serhalahmad/unibots/src/simulation/webots-files/main-env/april-tags/tag-0.png

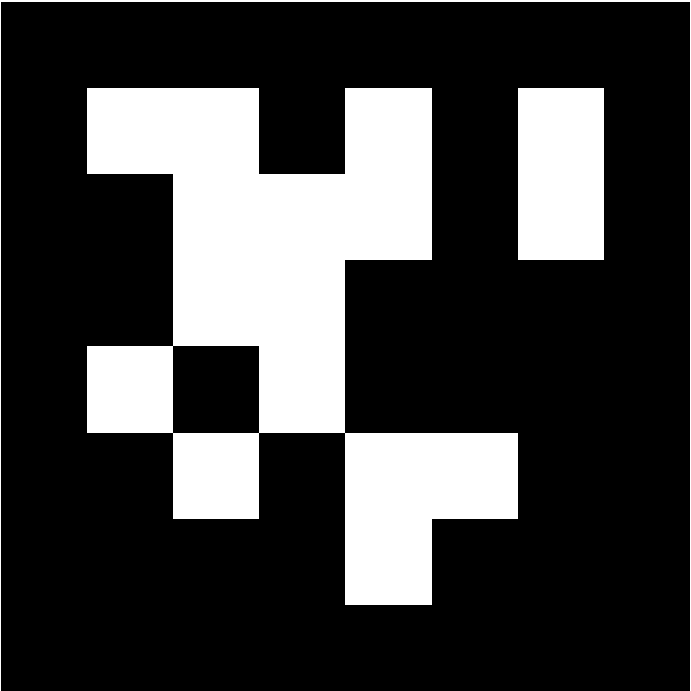
src/simulation/webots-files/main-env/april-tags/tag-0.png
