serhalahmad/unibots/src/simulation/webots-files/main-env/april-tags/tag-2.png

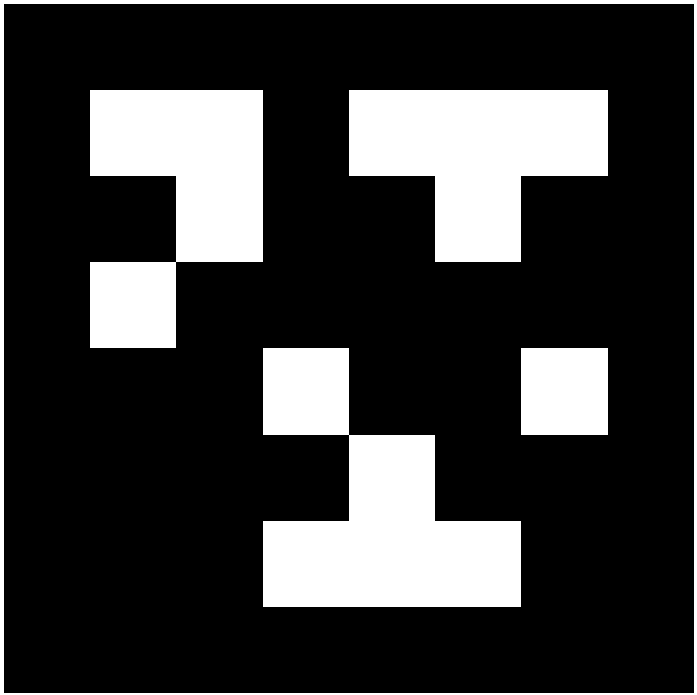
src/simulation/webots-files/main-env/april-tags/tag-2.png
