serhalahmad/unibots/src/simulation/webots-files/main-env/april-tags/tag-3.png

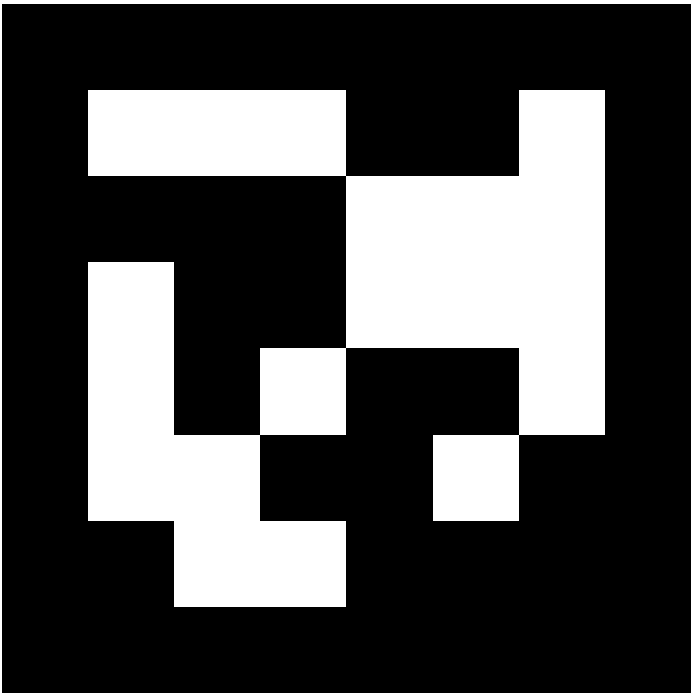
src/simulation/webots-files/main-env/april-tags/tag-3.png
