serhalahmad/unibots/src/simulation/webots-files/main-env/april-tags/tag-4.png

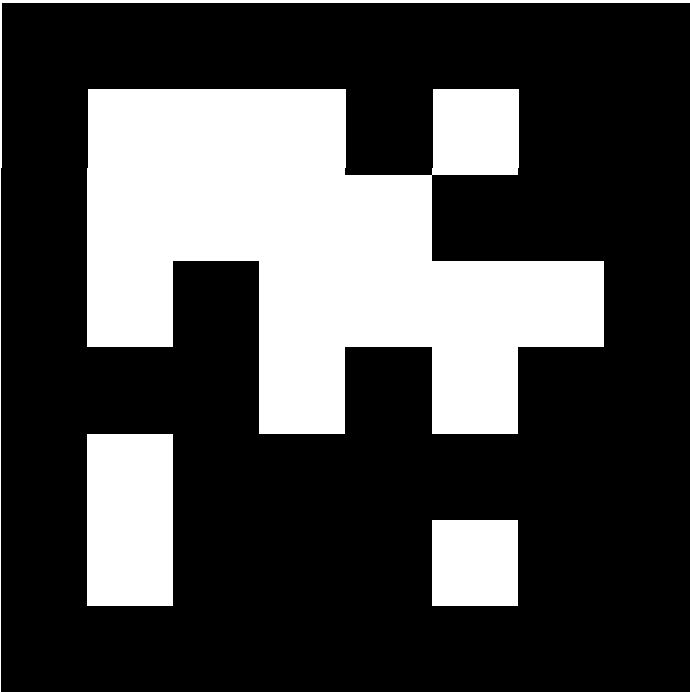
src/simulation/webots-files/main-env/april-tags/tag-4.png
