serhalahmad/unibots/src/simulation/webots-files/main-env/april-tags/tag-5.png

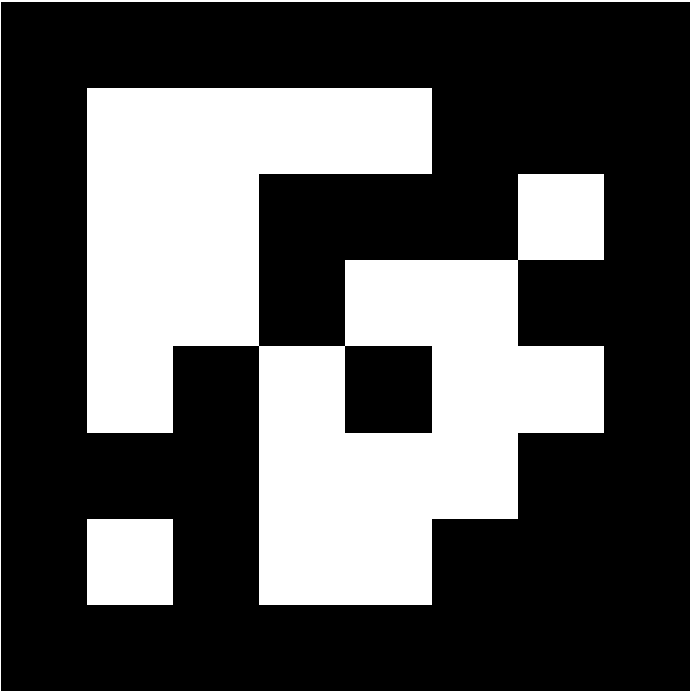
src/simulation/webots-files/main-env/april-tags/tag-5.png
