serhalahmad/unibots/src/simulation/webots-files/main-env/april-tags/tag-6.png

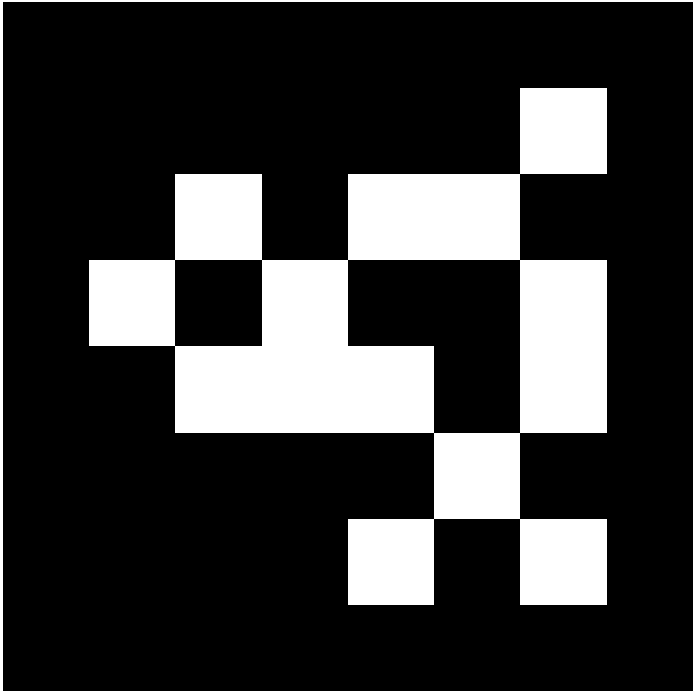
src/simulation/webots-files/main-env/april-tags/tag-6.png
