serhalahmad/unibots/src/simulation/webots-files/main-env/april-tags/tag-7.png

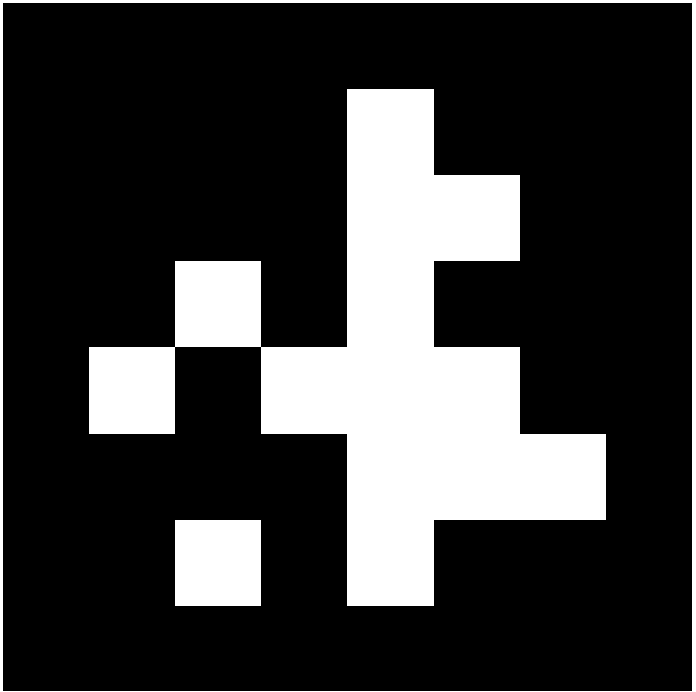
src/simulation/webots-files/main-env/april-tags/tag-7.png
