serhalahmad/unibots/src/simulation/webots-files/main-env/april-tags/tag-8.png

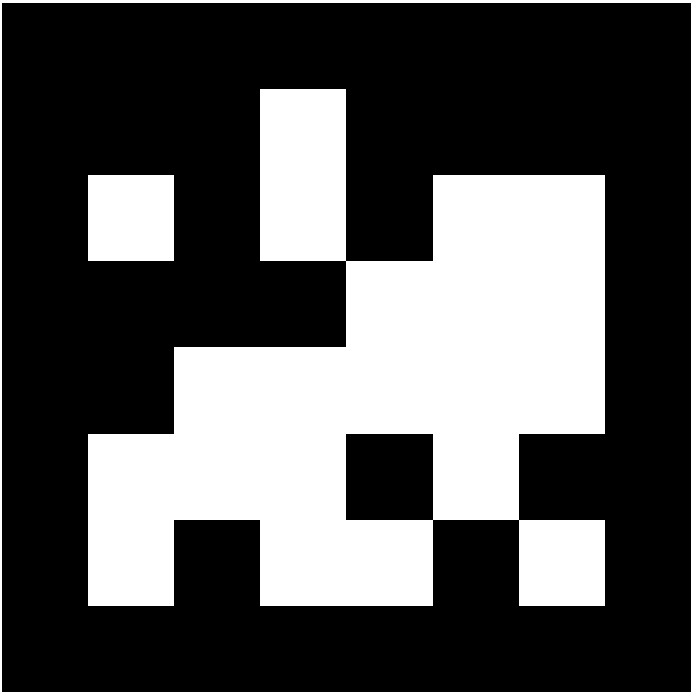
src/simulation/webots-files/main-env/april-tags/tag-8.png
