serhalahmad/unibots/src/simulation/webots-files/main-env/april-tags/tag-9.png

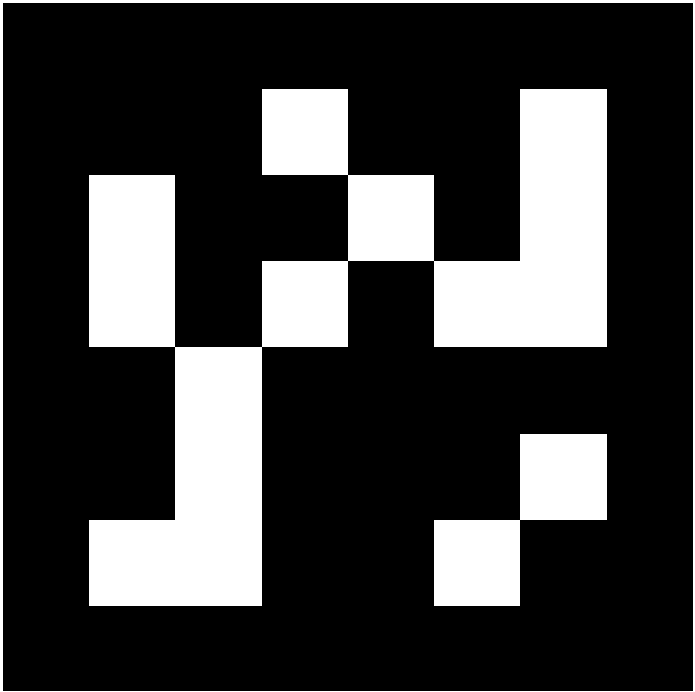
src/simulation/webots-files/main-env/april-tags/tag-9.png
