serhalahmad/unibots/src/simulation/webots-files/main-env/april-tags/tag-10.png

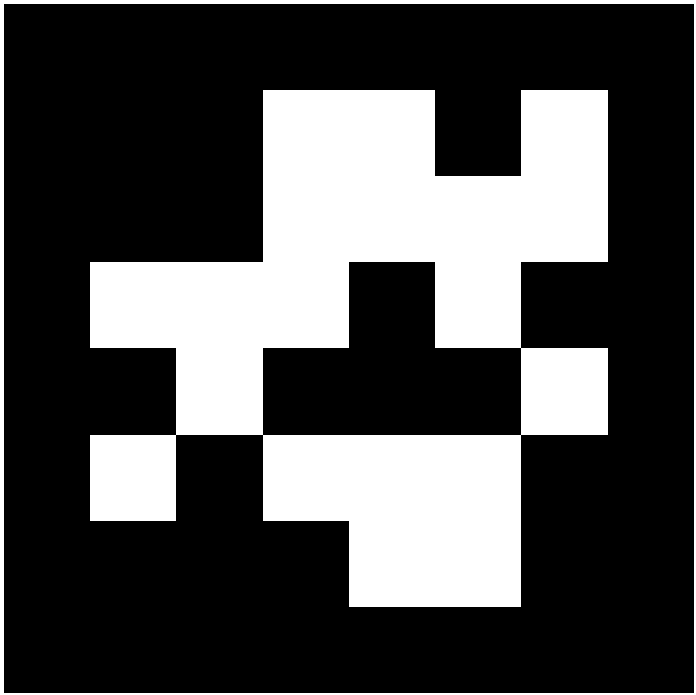
src/simulation/webots-files/main-env/april-tags/tag-10.png
