serhalahmad/unibots/src/simulation/webots-files/main-env/april-tags/tag-11.png

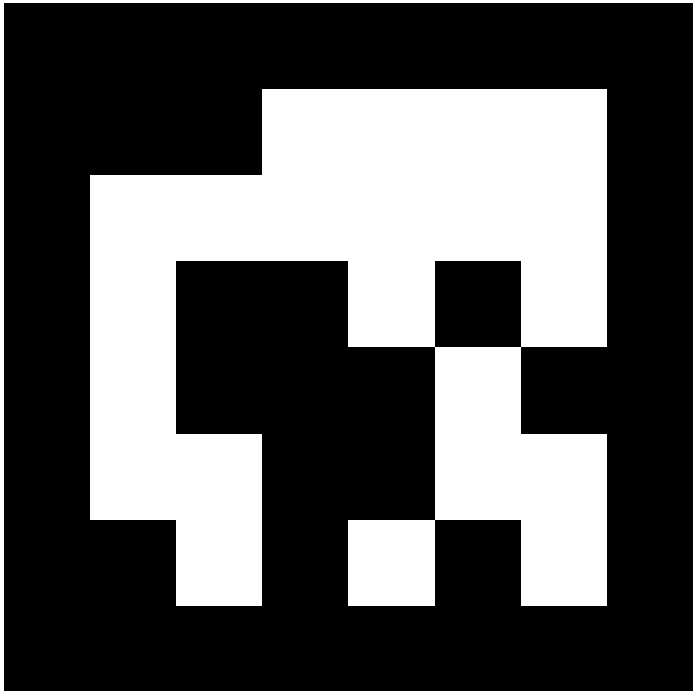
src/simulation/webots-files/main-env/april-tags/tag-11.png
