serhalahmad/unibots/src/simulation/webots-files/main-env/april-tags/tag-12.png

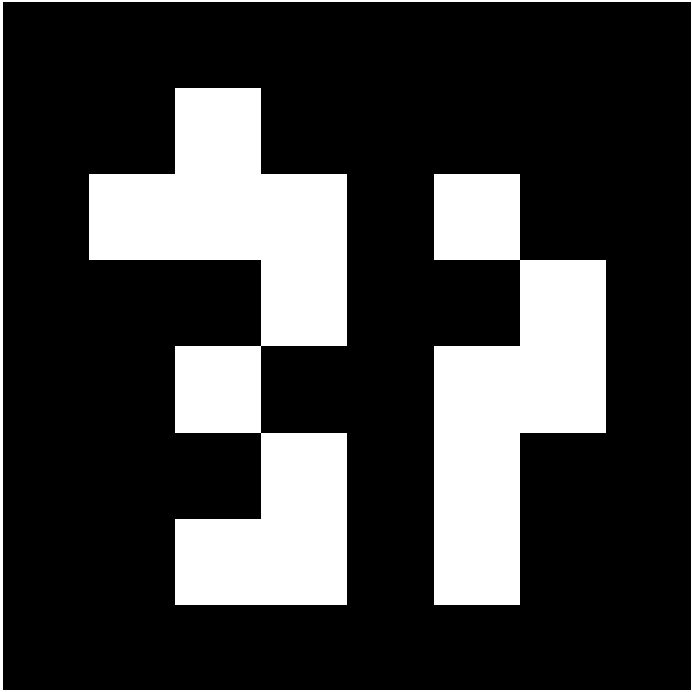
src/simulation/webots-files/main-env/april-tags/tag-12.png
