serhalahmad/unibots/src/simulation/webots-files/main-env/april-tags/tag-14.png

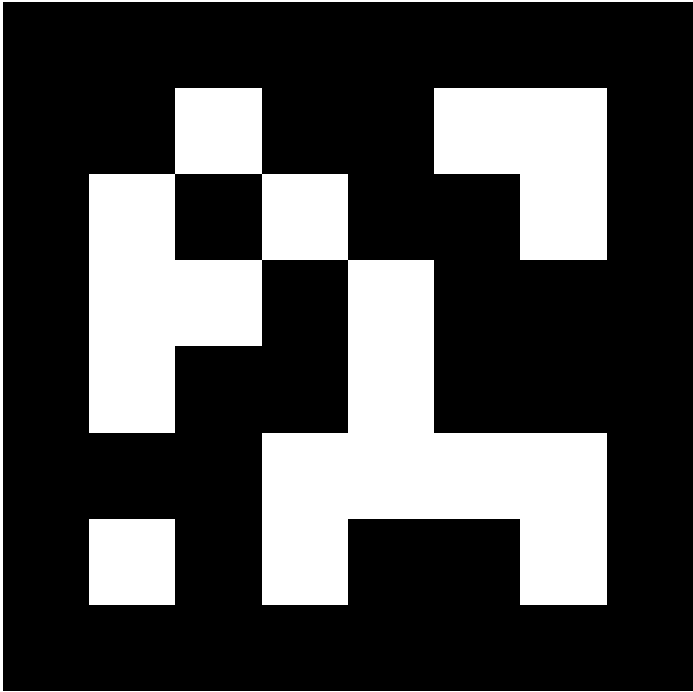
src/simulation/webots-files/main-env/april-tags/tag-14.png
