serhalahmad/unibots/src/simulation/webots-files/main-env/april-tags/tag-15.png

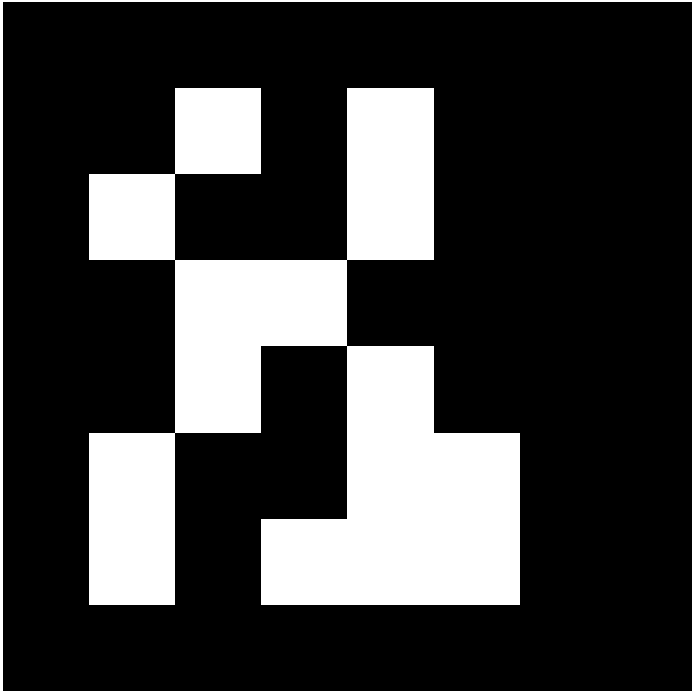
src/simulation/webots-files/main-env/april-tags/tag-15.png
