serhalahmad/unibots/src/simulation/webots-files/main-env/april-tags/tag-17.png

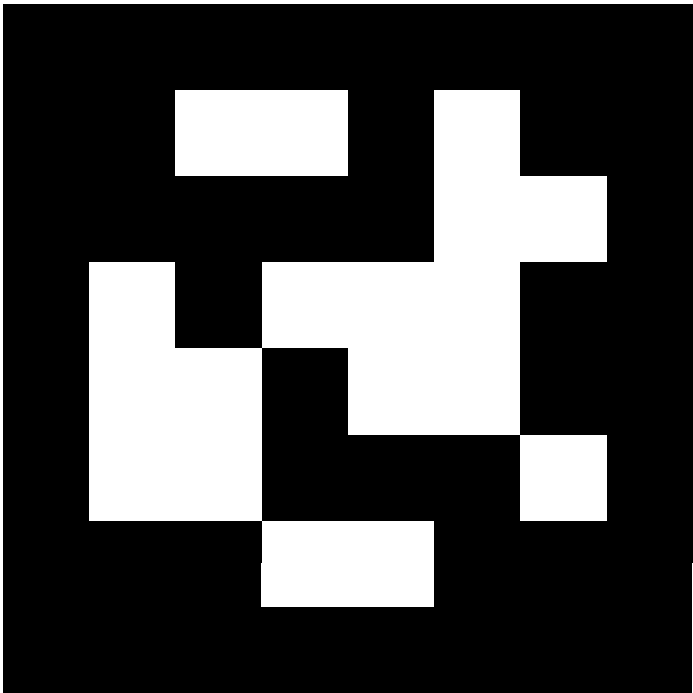
src/simulation/webots-files/main-env/april-tags/tag-17.png
