serhalahmad/unibots/src/simulation/webots-files/main-env/april-tags/tag-18.png

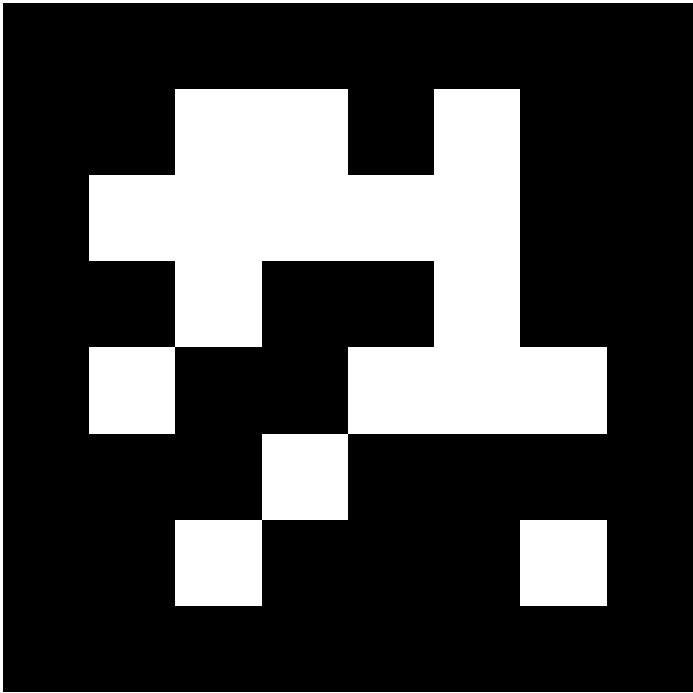
src/simulation/webots-files/main-env/april-tags/tag-18.png
