serhalahmad/unibots/src/simulation/webots-files/main-env/april-tags/tag-19.png

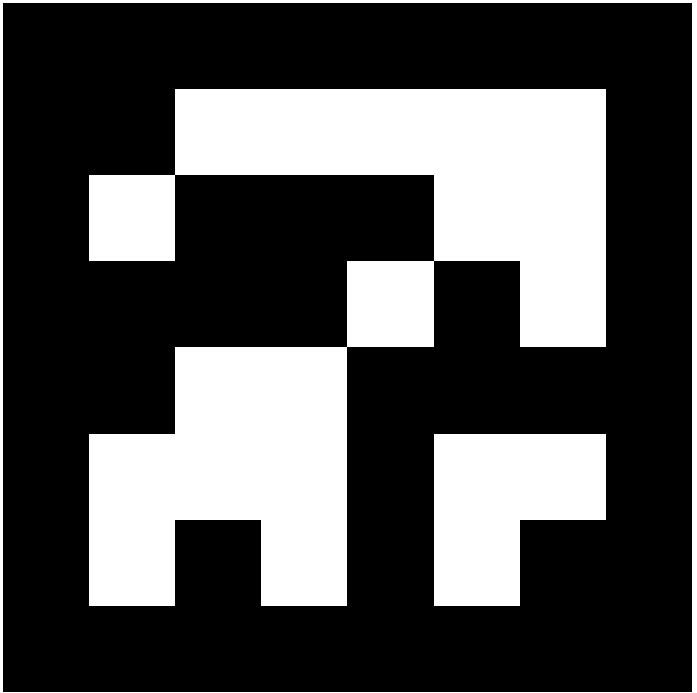
src/simulation/webots-files/main-env/april-tags/tag-19.png
