serhalahmad/unibots/src/simulation/webots-files/main-env/april-tags/tag-20.png

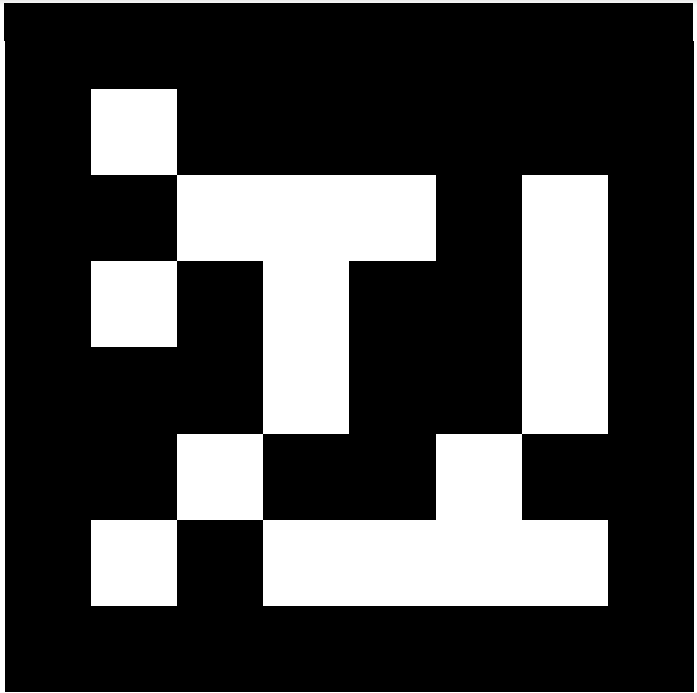
src/simulation/webots-files/main-env/april-tags/tag-20.png
