serhalahmad/unibots/src/simulation/webots-files/main-env/april-tags/tag-22.png

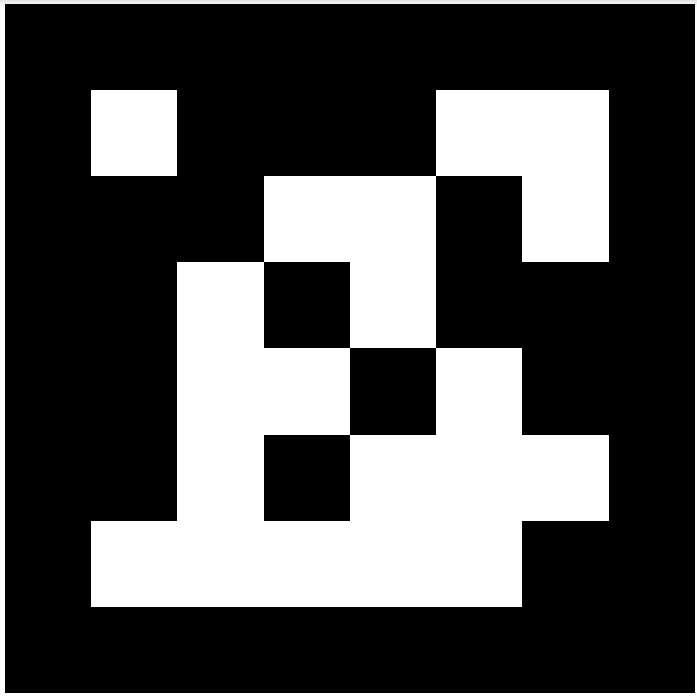
src/simulation/webots-files/main-env/april-tags/tag-22.png
