serhalahmad/unibots/cad-files/servo/mg-996r-servo-motor-1.snapshot.23/Parts/MG996R Motor.SLDPRT

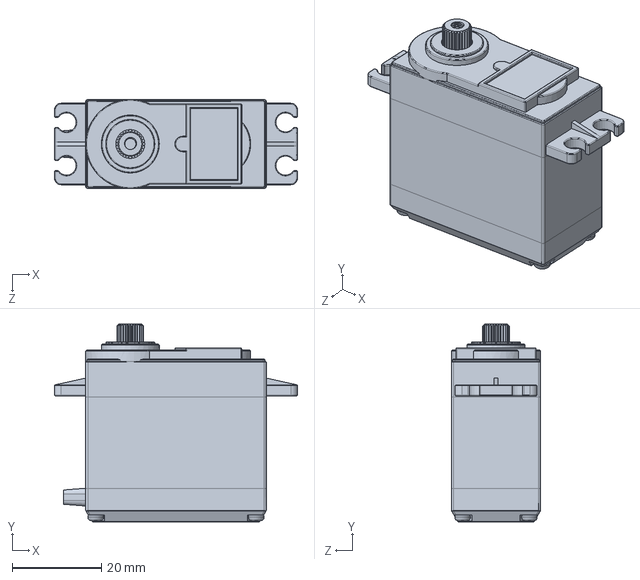
[picture p48: CAD file, 2025-01-23]
cad-files/servo/mg-996r-servo-motor-1.snapshot.23/Parts/MG996R Motor.SLDPRT
54.5 x 44.4 x 20.0 mm
