serhalahmad/unibots/cad-files/tire.SLDPRT

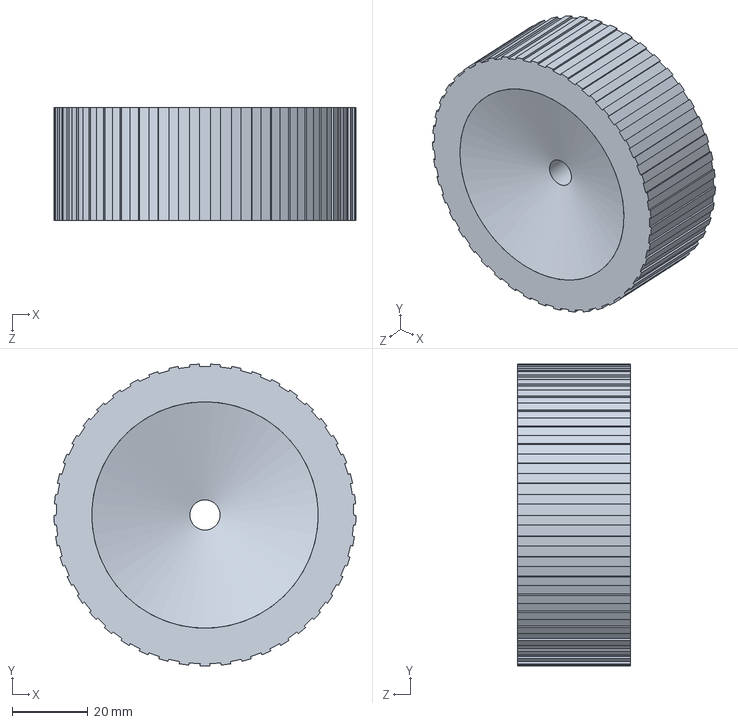
[picture p49: CAD file, 2025-01-23]
cad-files/tire.SLDPRT
80.0 x 80.0 x 30.0 mm
