serhalahmad/unibots/cad-files/unibots chassis/beam.STL.SLDPRT

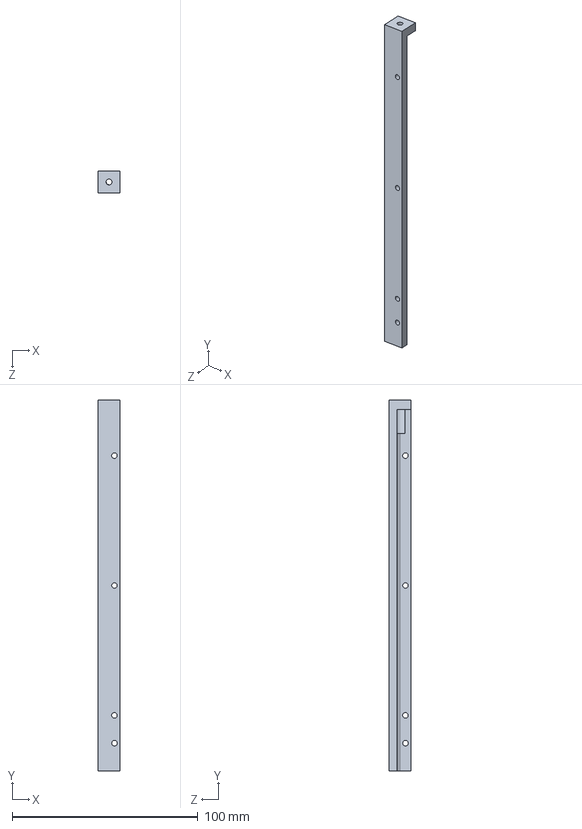
[picture p50: CAD file, 2025-03-25]
cad-files/unibots chassis/beam.STL.SLDPRT
12.0 x 200.0 x 12.0 mm
