serhalahmad/unibots/cad-files/unibots chassis/dxf files/componentsfloor.DXF

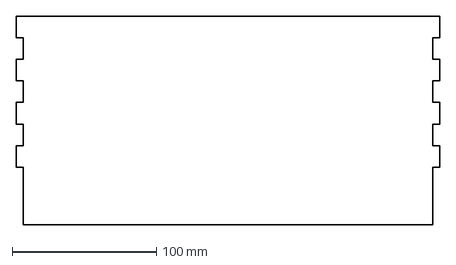
[picture p51: CAD file, 2025-03-25]
cad-files/unibots chassis/dxf files/componentsfloor.DXF
294.0 x 145.0 mm
