serhalahmad/unibots/cad-files/unibots v1/tire og.SLDPRT

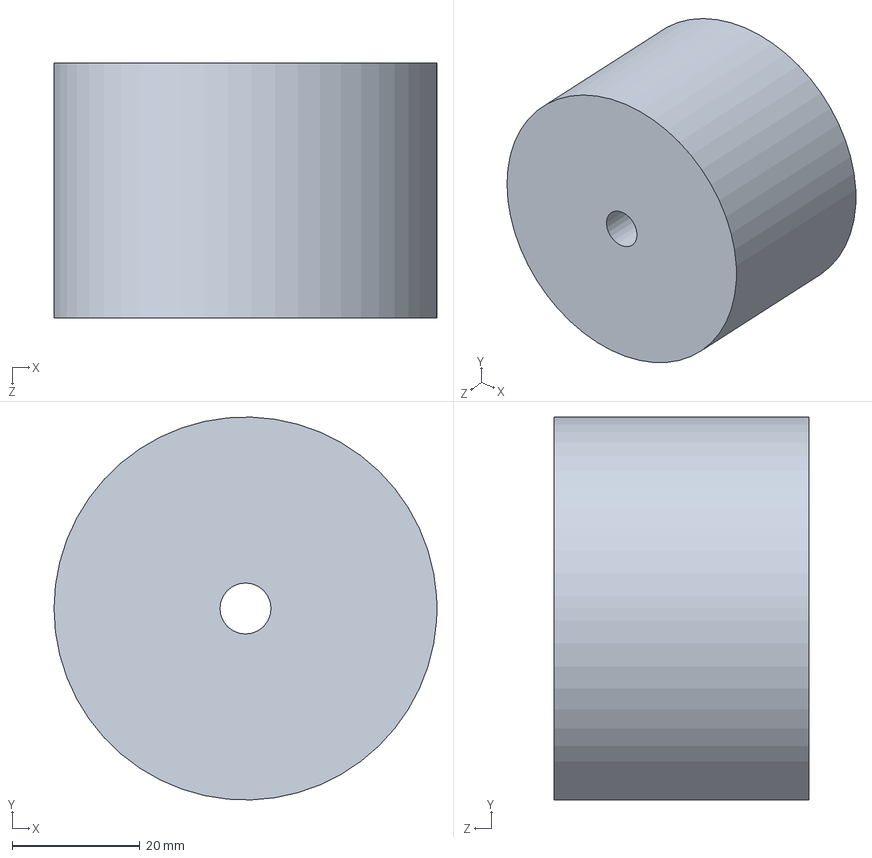
[picture p52: CAD file, 2025-01-23]
cad-files/unibots v1/tire og.SLDPRT
60.0 x 60.0 x 40.0 mm
