serhalahmad/unibots/src/simulation/webots-files/main-env/objects/rugby-ball.obj

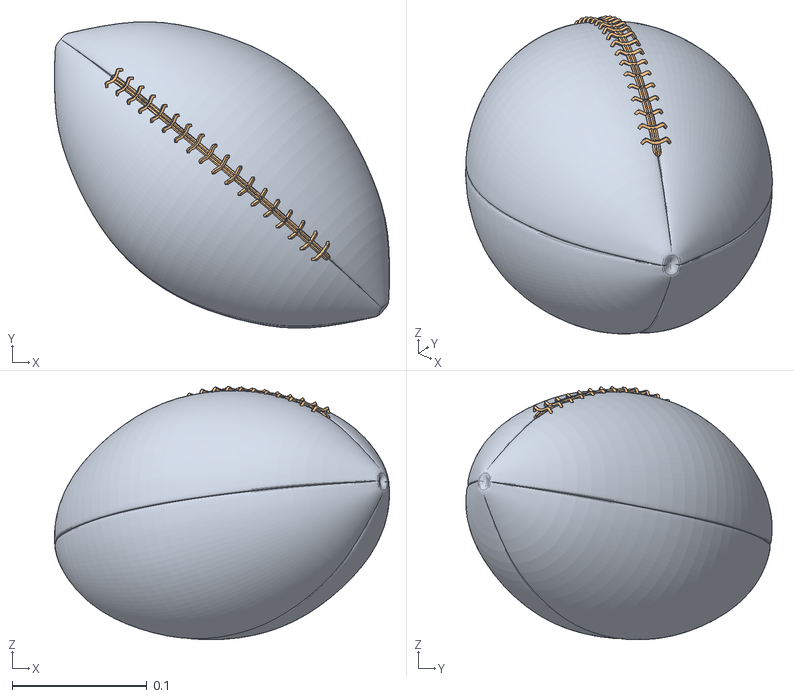
[picture p53: CAD file, 2025-06-17]
src/simulation/webots-files/main-env/objects/rugby-ball.obj
0.249 x 0.228 x 0.188
American_Football_ball_1_Cylinder
American_Football_ball_2_BezierCurve
