serhalahmad/unibots/cad-files/gearbox test/Part4.SLDPRT

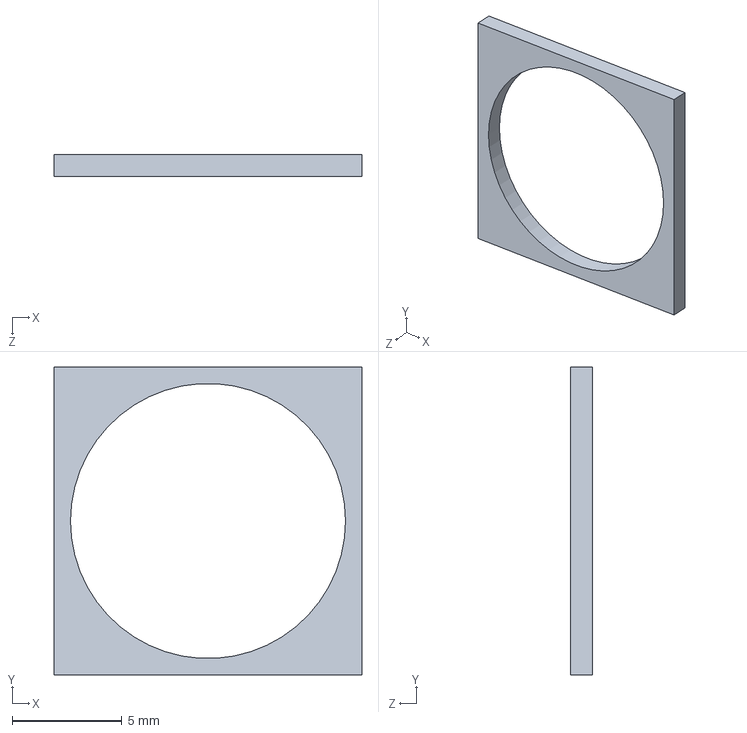
[picture p54: CAD file, 2025-02-14]
cad-files/gearbox test/Part4.SLDPRT
14.0 x 14.0 x 1.00 mm
