serhalahmad/unibots/cad-files/motor/worm-gear-motor-high-torque-12v-dc-motor-1.snapshot.1/Worm Gear Motor.SLDPRT

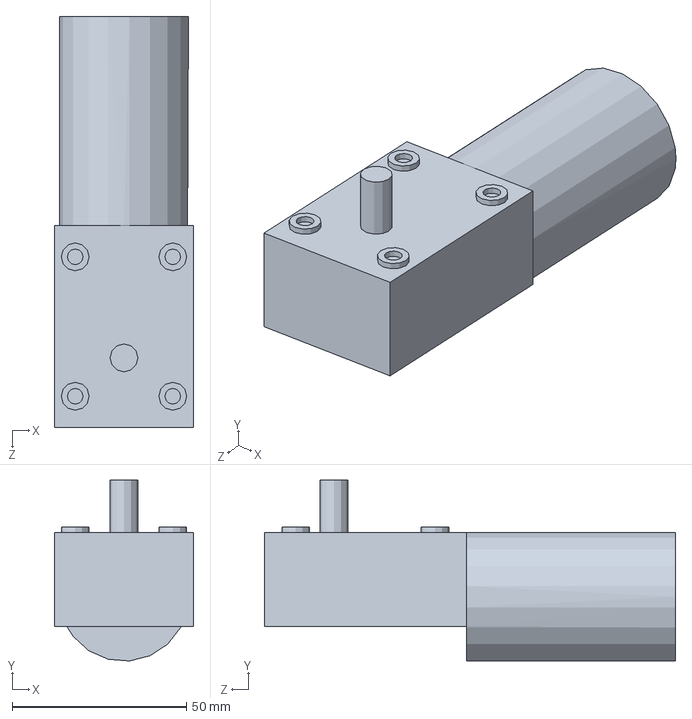
[picture p55: CAD file, 2025-01-23]
cad-files/motor/worm-gear-motor-high-torque-12v-dc-motor-1.snapshot.1/Worm Gear Motor.SLDPRT
40.0 x 51.9 x 118.0 mm
