serhalahmad/unibots/cad-files/New folder/chassis.STL

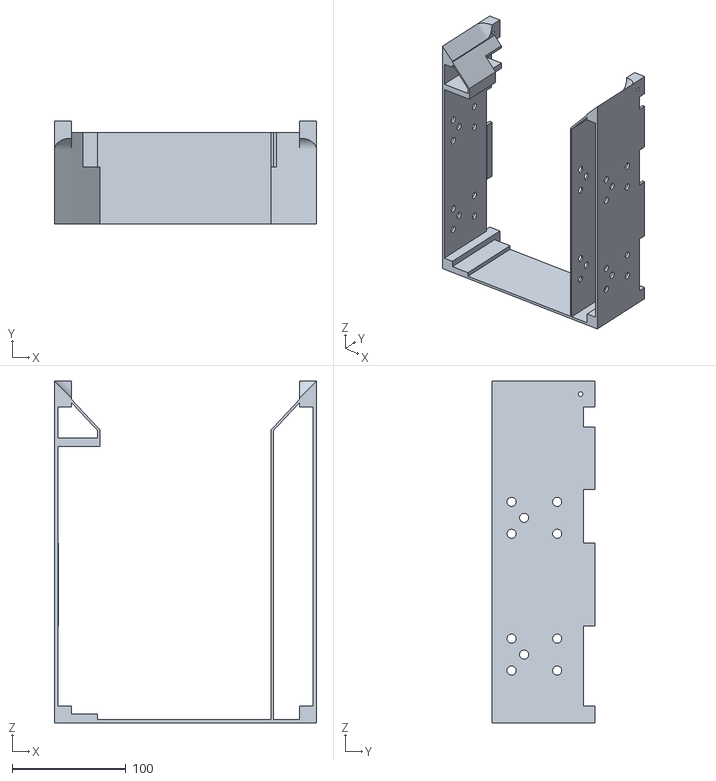
[picture p56: CAD file, 2025-01-28]
cad-files/New folder/chassis.STL
230.0 x 90.0 x 300.0
