serhalahmad/unibots/cad-files/servo/mg-996r-servo-motor-1.snapshot.23/Parts/circular horn.SLDPRT

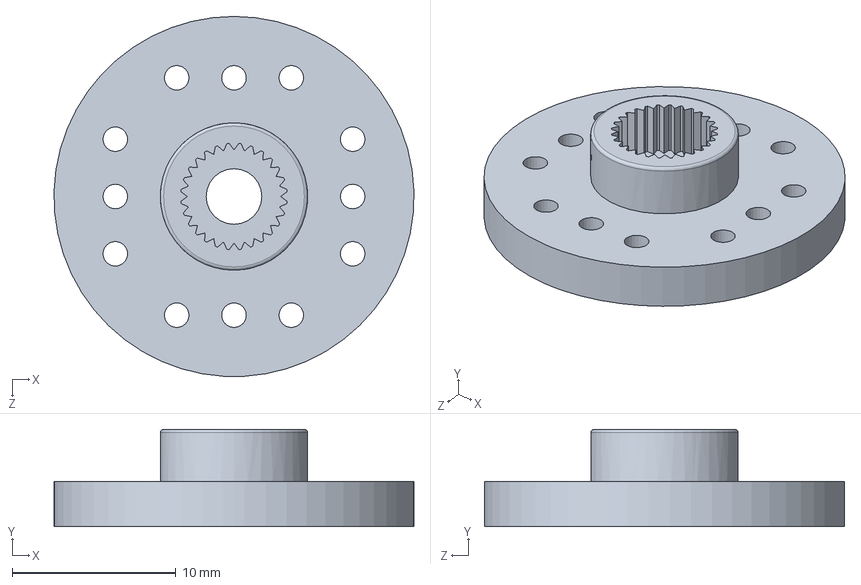
[picture p57: CAD file, 2025-01-23]
cad-files/servo/mg-996r-servo-motor-1.snapshot.23/Parts/circular horn.SLDPRT
22.0 x 5.95 x 22.0 mm
