serhalahmad/unibots/cad-files/unibots chassis/dxf files/rugbywall2.DXF

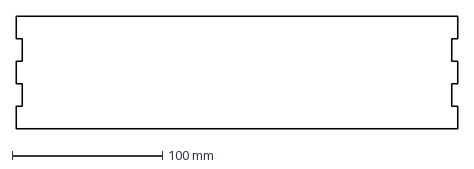
[picture p58: CAD file, 2025-03-25]
cad-files/unibots chassis/dxf files/rugbywall2.DXF
294.0 x 75.0 mm
