serhalahmad/unibots/cad-files/unibots chassis/rugbywall1.SLDPRT

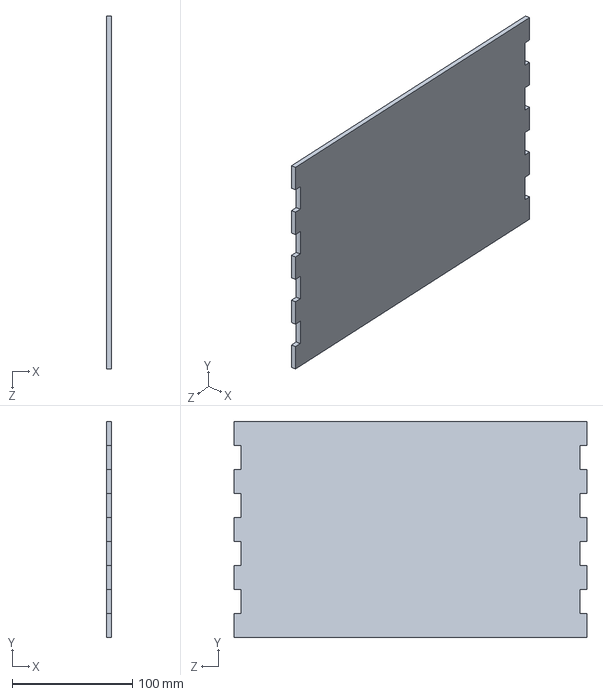
[picture p59: CAD file, 2025-03-25]
cad-files/unibots chassis/rugbywall1.SLDPRT
4.00 x 180.0 x 294.0 mm
