serhalahmad/unibots/cad-files/unibots v1/testclamp.SLDPRT

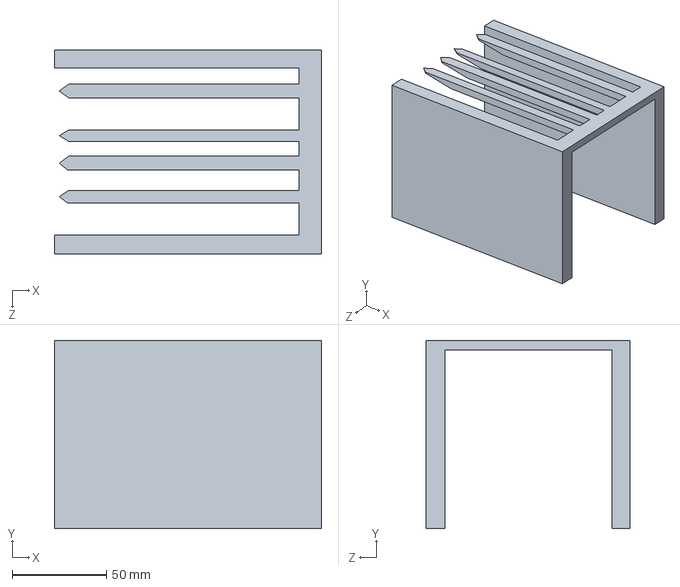
[picture p60: CAD file, 2025-01-23]
cad-files/unibots v1/testclamp.SLDPRT
141.8 x 100.0 x 108.3 mm
