serhalahmad/unibots/cad-files/door.SLDPRT

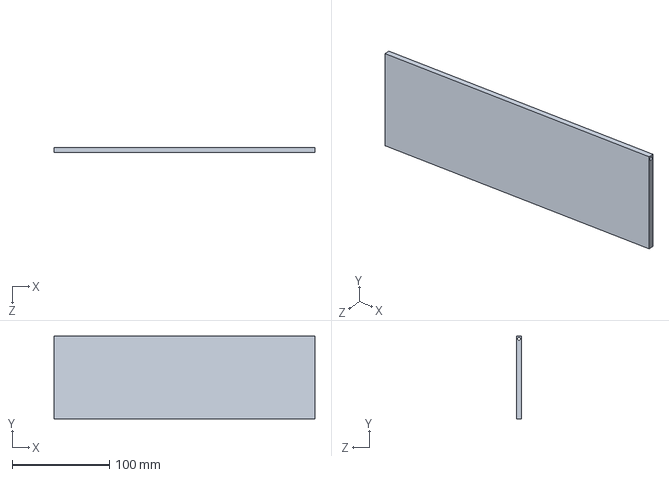
[picture p61: CAD file, 2025-01-23]
cad-files/door.SLDPRT
268.0 x 85.0 x 5.00 mm
