serhalahmad/unibots/cad-files/gearbox test/6_30mm shaft.STL

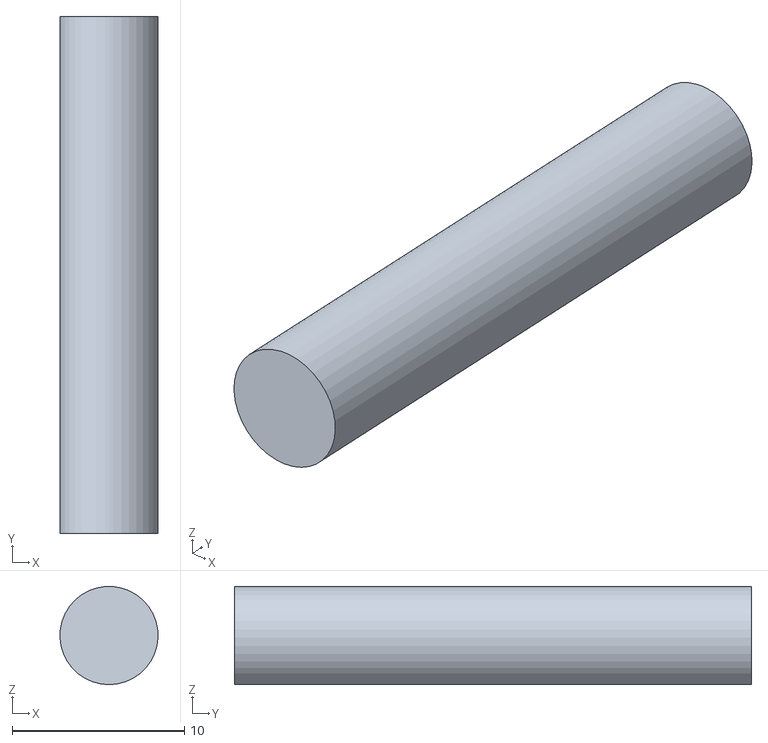
[picture p62: CAD file, 2025-02-14]
cad-files/gearbox test/6_30mm shaft.STL
5.69 x 30.0 x 5.70
