serhalahmad/unibots/cad-files/servo/mg-996r-servo-motor-1.snapshot.23/Parts/2-star horn.SLDPRT

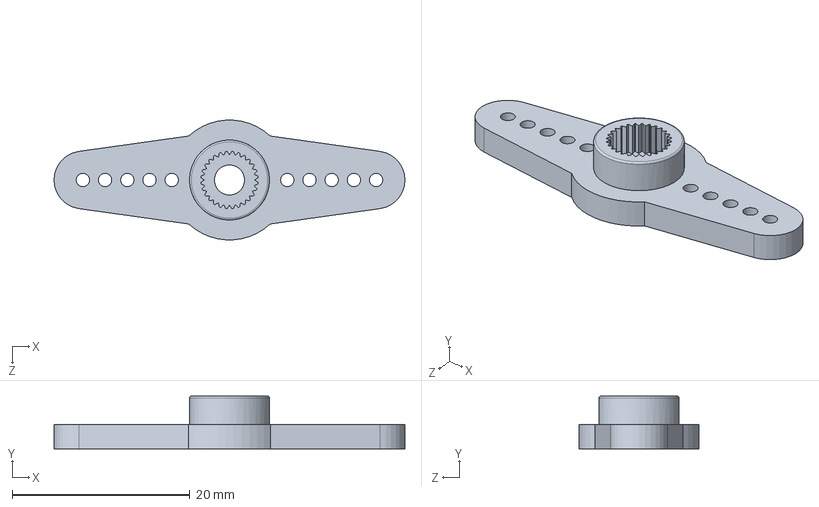
[picture p63: CAD file, 2025-01-23]
cad-files/servo/mg-996r-servo-motor-1.snapshot.23/Parts/2-star horn.SLDPRT
39.5 x 5.95 x 13.5 mm
