serhalahmad/unibots/cad-files/unibots chassis/dxf files/sidewalls.DXF

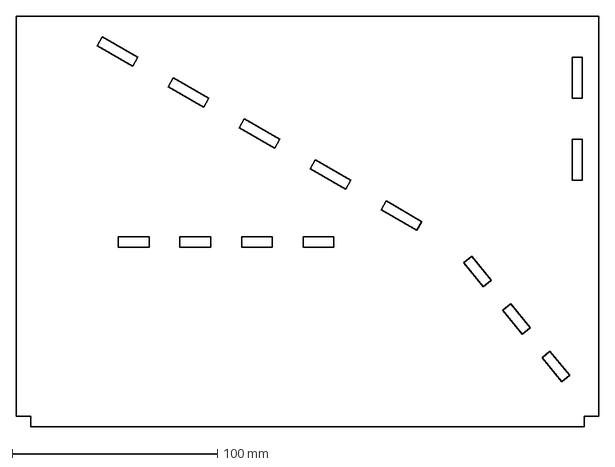
[picture p64: CAD file, 2025-03-25]
cad-files/unibots chassis/dxf files/sidewalls.DXF
284.0 x 200.0 mm
