serhalahmad/unibots/cad-files/17_1_25 rugby.SLDPRT

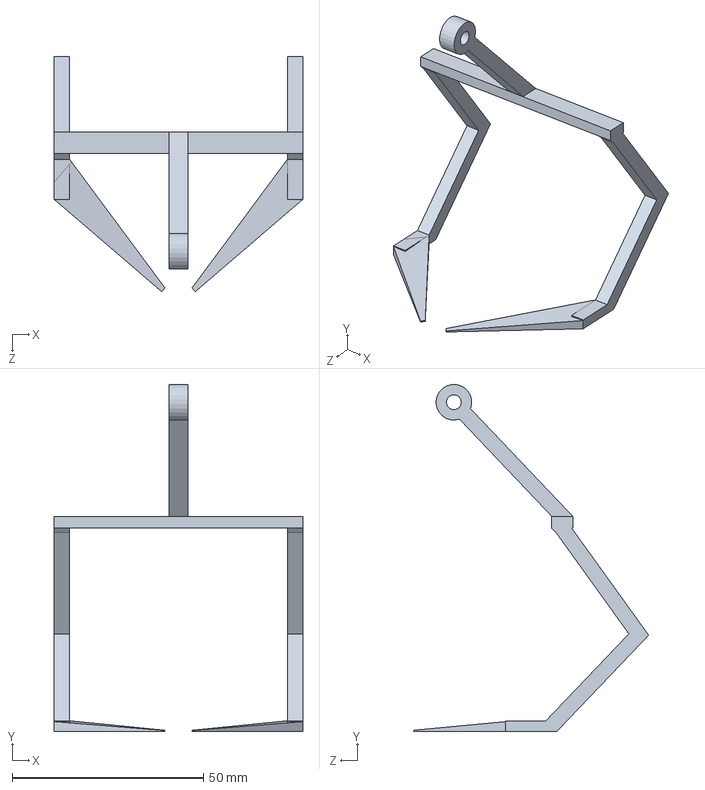
[picture p65: CAD file, 2025-01-23]
cad-files/17_1_25 rugby.SLDPRT
65.0 x 90.8 x 61.6 mm
