serhalahmad/unibots/cad-files/unibots chassis/layer1plate.SLDPRT

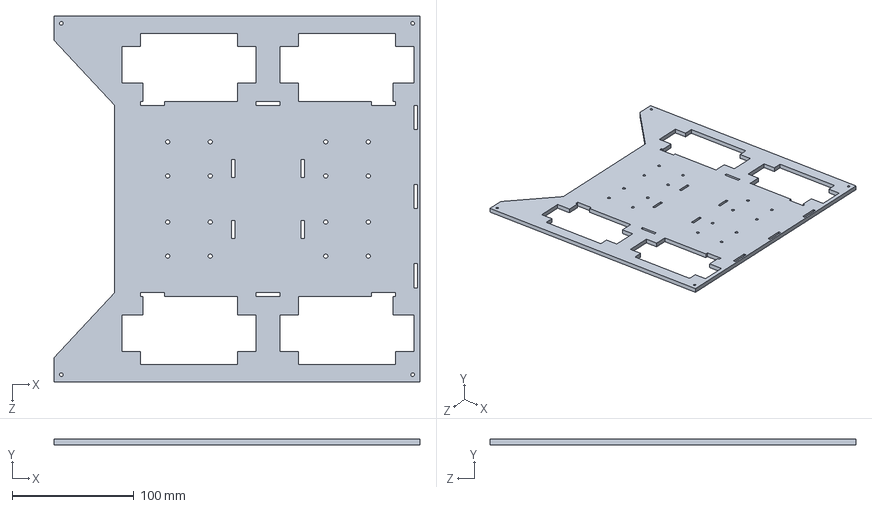
[picture p66: CAD file, 2025-03-25]
cad-files/unibots chassis/layer1plate.SLDPRT
301.0 x 5.00 x 301.0 mm
