serhalahmad/unibots/cad-files/gearbox test/SPURGEAR20TEETH.SLDPRT

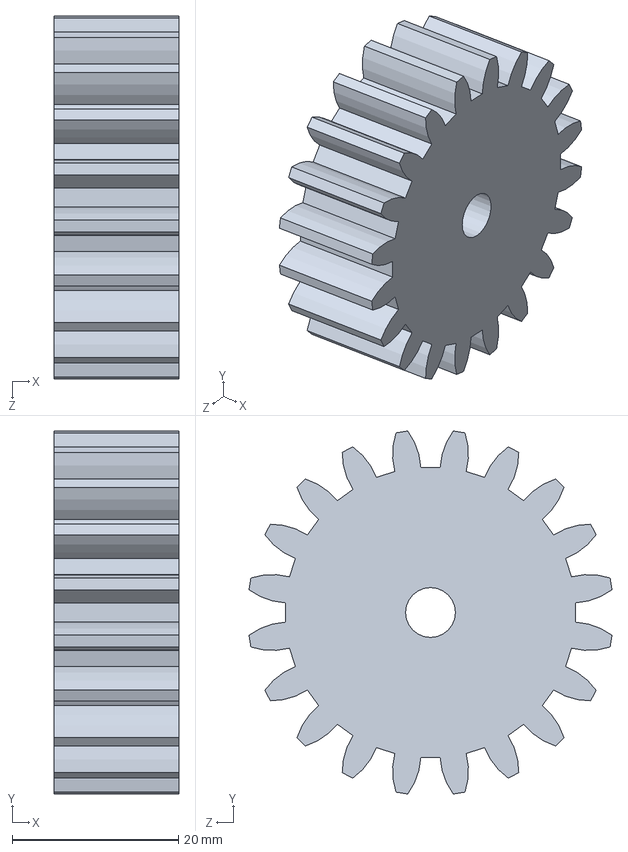
[picture p67: CAD file, 2025-02-14]
cad-files/gearbox test/SPURGEAR20TEETH.SLDPRT
15.0 x 43.7 x 43.7 mm
