serhalahmad/unibots/cad-files/servo/mg-996r-servo-motor-1.snapshot.23/Parts/6-star horn.SLDPRT

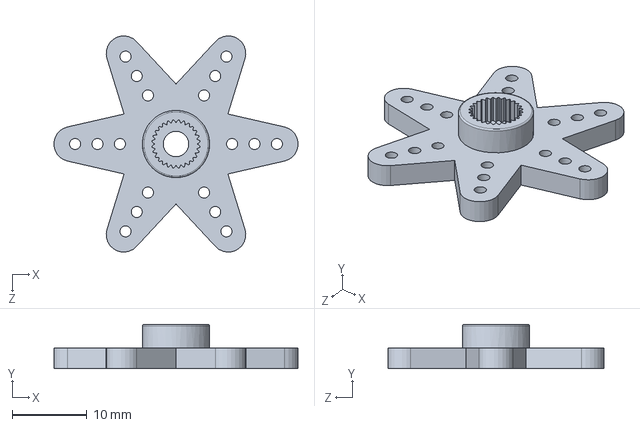
[picture p68: CAD file, 2025-01-23]
cad-files/servo/mg-996r-servo-motor-1.snapshot.23/Parts/6-star horn.SLDPRT
32.6 x 5.95 x 28.9 mm
