serhalahmad/unibots/cad-files/trial door.SLDPRT

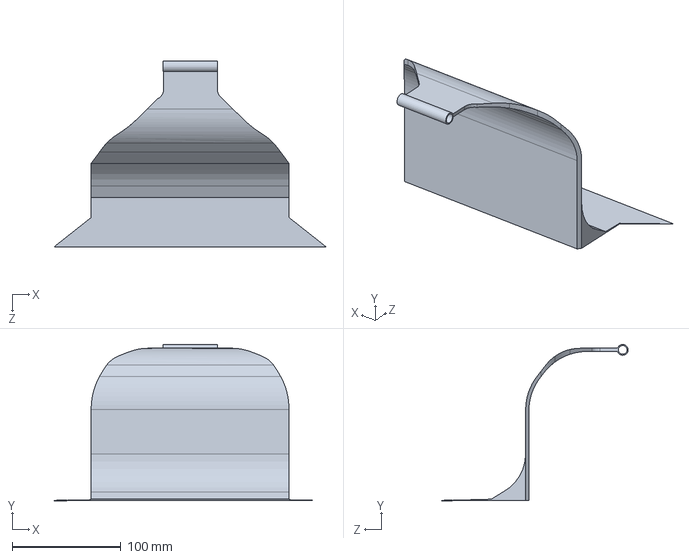
[picture p69: CAD file, 2025-01-23]
cad-files/trial door.SLDPRT
250.0 x 143.5 x 171.2 mm
