serhalahmad/unibots/cad-files/unibots chassis/trapmechpart1.SLDPRT

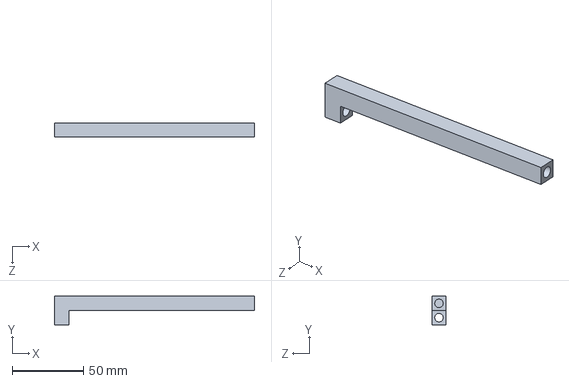
[picture p70: CAD file, 2025-03-25]
cad-files/unibots chassis/trapmechpart1.SLDPRT
140.0 x 20.0 x 10.0 mm
