serhalahmad/unibots/cad-files/unibots v1/trialdoorv2.SLDPRT

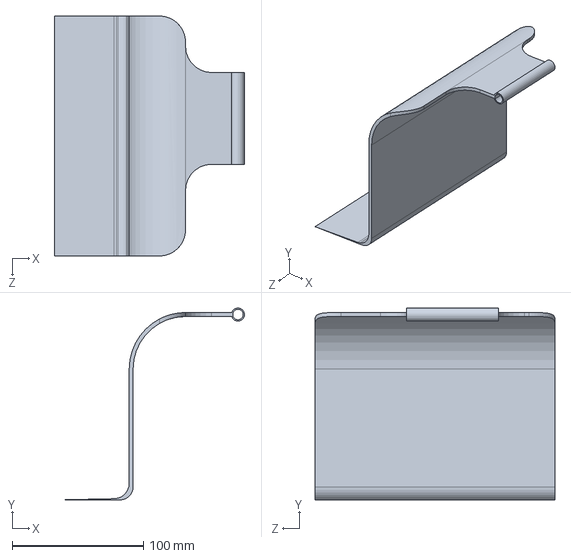
[picture p71: CAD file, 2025-01-23]
cad-files/unibots v1/trialdoorv2.SLDPRT
145.0 x 146.5 x 183.1 mm
