serhalahmad/unibots/cad-files/servo/mg-996r-servo-motor-1.snapshot.23/Parts/4-star horn.SLDPRT

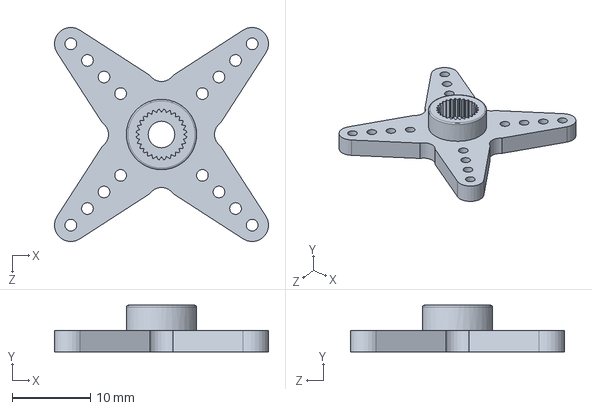
[picture p72: CAD file, 2025-01-23]
cad-files/servo/mg-996r-servo-motor-1.snapshot.23/Parts/4-star horn.SLDPRT
27.4 x 5.95 x 27.4 mm
