serhalahmad/unibots/cad-files/unibots chassis/pingpong-bacjwall.SLDPRT

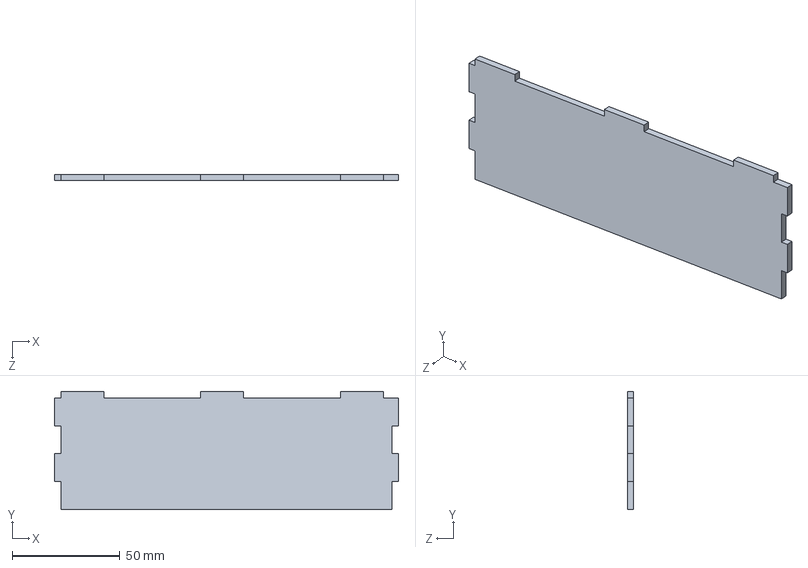
[picture p73: CAD file, 2025-03-25]
cad-files/unibots chassis/pingpong-bacjwall.SLDPRT
160.0 x 55.0 x 3.00 mm
