serhalahmad/unibots/cad-files/unibots v1/trial door.SLDPRT

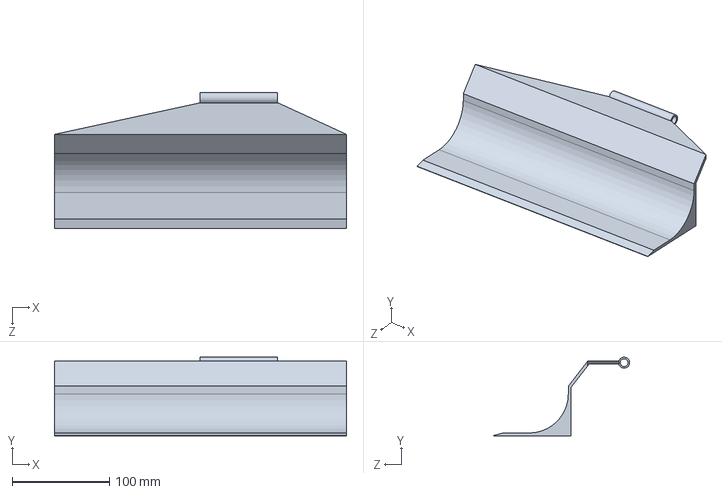
[picture p74: CAD file, 2025-01-23]
cad-files/unibots v1/trial door.SLDPRT
300.0 x 80.9 x 140.1 mm
