serhalahmad/unibots/cad-files/gearbox test/mountin.SLDPRT

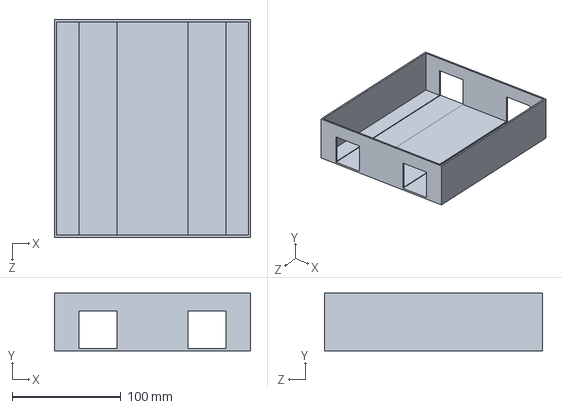
[picture p75: CAD file, 2025-02-14]
cad-files/gearbox test/mountin.SLDPRT
180.0 x 53.0 x 200.0 mm
