serhalahmad/unibots/cad-files/layer1cover.SLDPRT

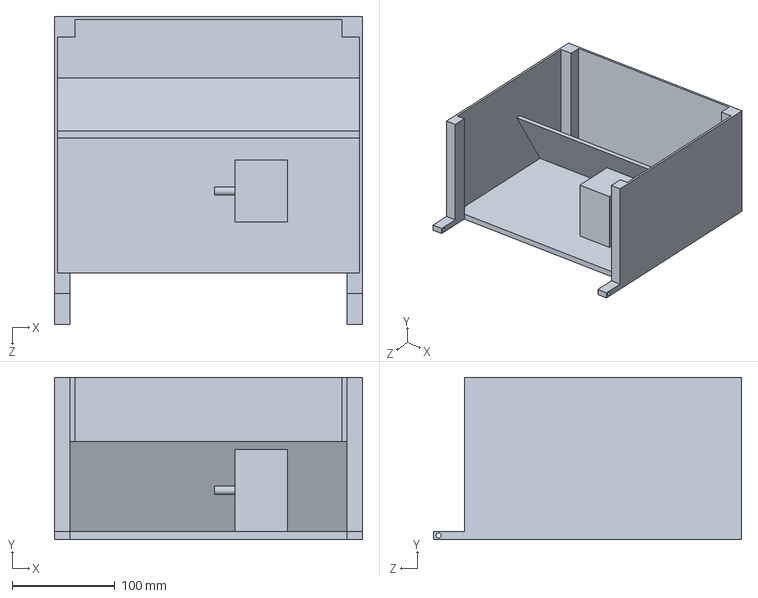
[picture p76: CAD file, 2025-01-23]
cad-files/layer1cover.SLDPRT
300.0 x 158.0 x 300.0 mm
