serhalahmad/unibots/cad-files/unibots chassis/diagonallwall2.SLDPRT

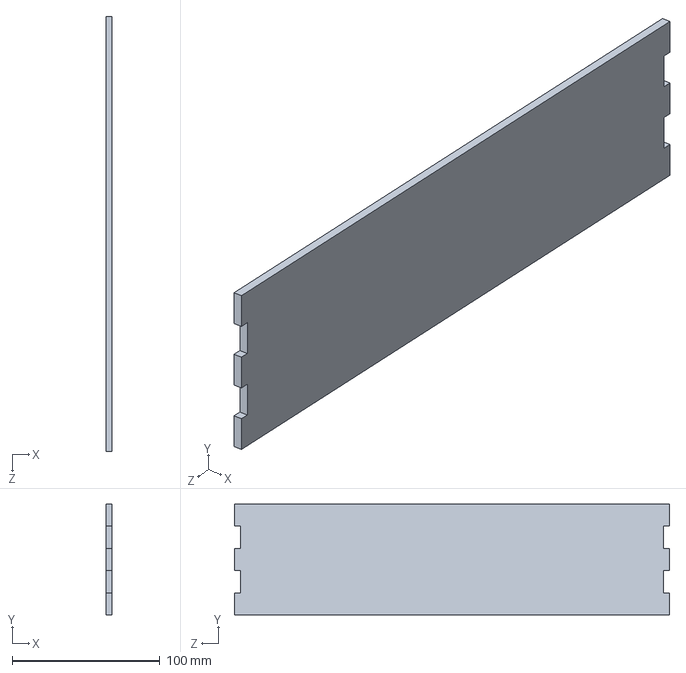
[picture p77: CAD file, 2025-03-25]
cad-files/unibots chassis/diagonallwall2.SLDPRT
4.00 x 75.0 x 294.0 mm
