serhalahmad/unibots/cad-files/unibots chassis/left-right wall.SLDPRT

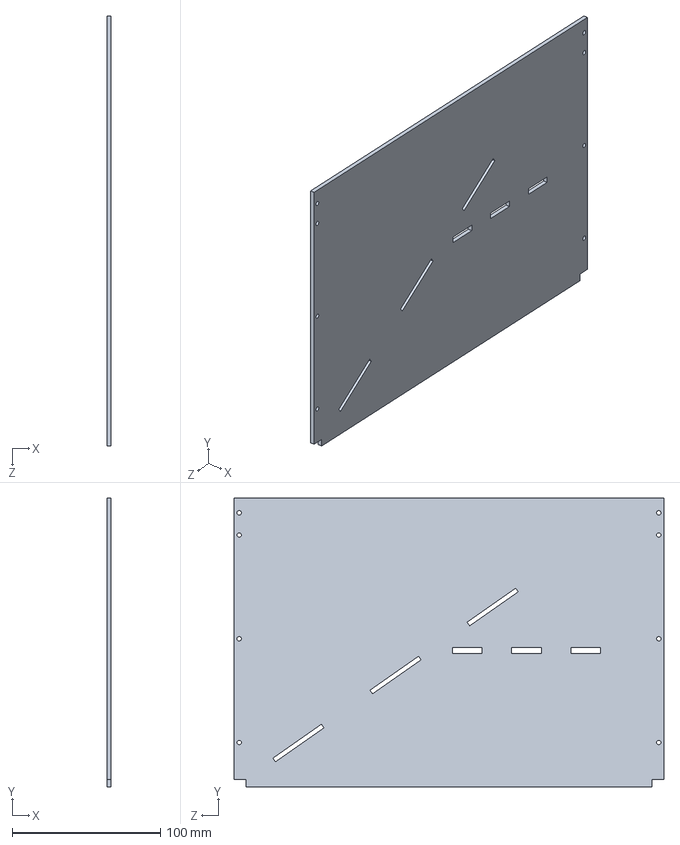
[picture p78: CAD file, 2025-03-25]
cad-files/unibots chassis/left-right wall.SLDPRT
3.00 x 195.0 x 290.0 mm
