serhalahmad/unibots/cad-files/unibots v1/testclamp2.SLDPRT

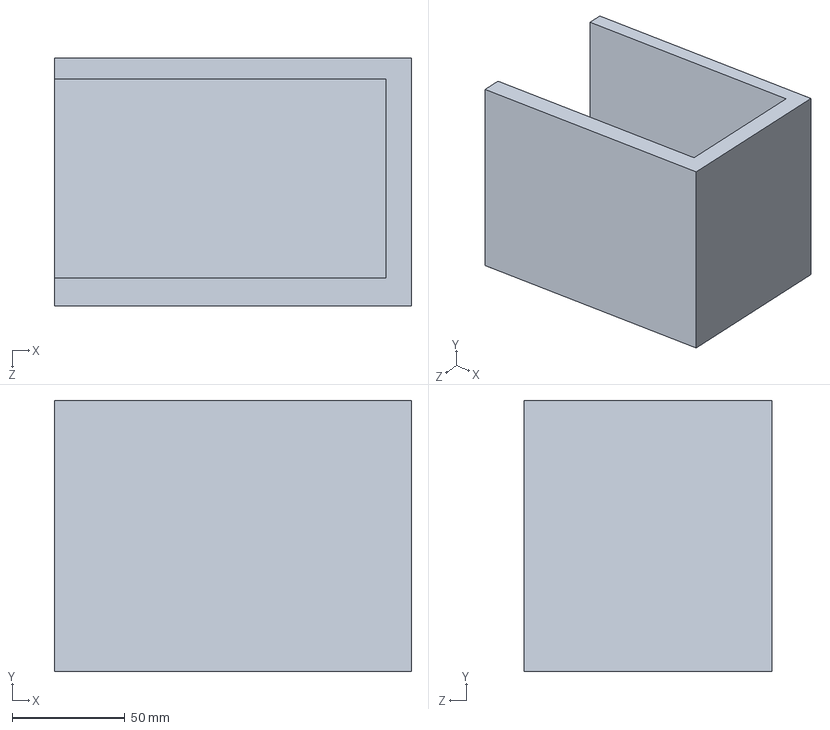
[picture p79: CAD file, 2025-01-23]
cad-files/unibots v1/testclamp2.SLDPRT
158.1 x 120.0 x 110.0 mm
