serhalahmad/unibots/cad-files/unibots v1/layer1cover og.SLDPRT

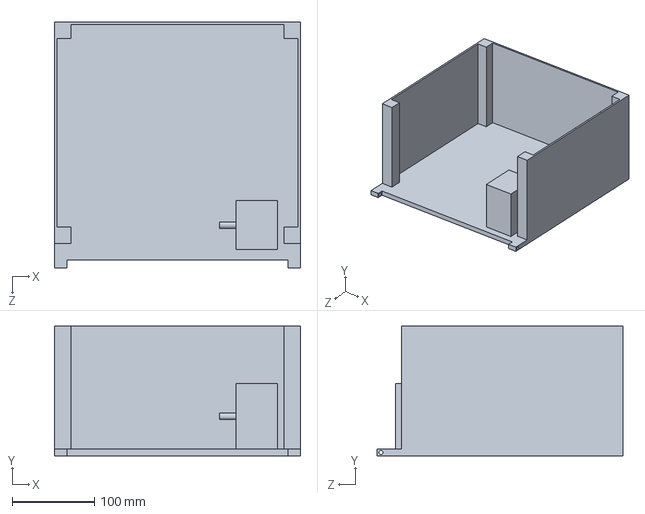
[picture p80: CAD file, 2025-01-23]
cad-files/unibots v1/layer1cover og.SLDPRT
300.0 x 158.0 x 300.0 mm
