serhalahmad/unibots/cad-files/chassis.SLDPRT

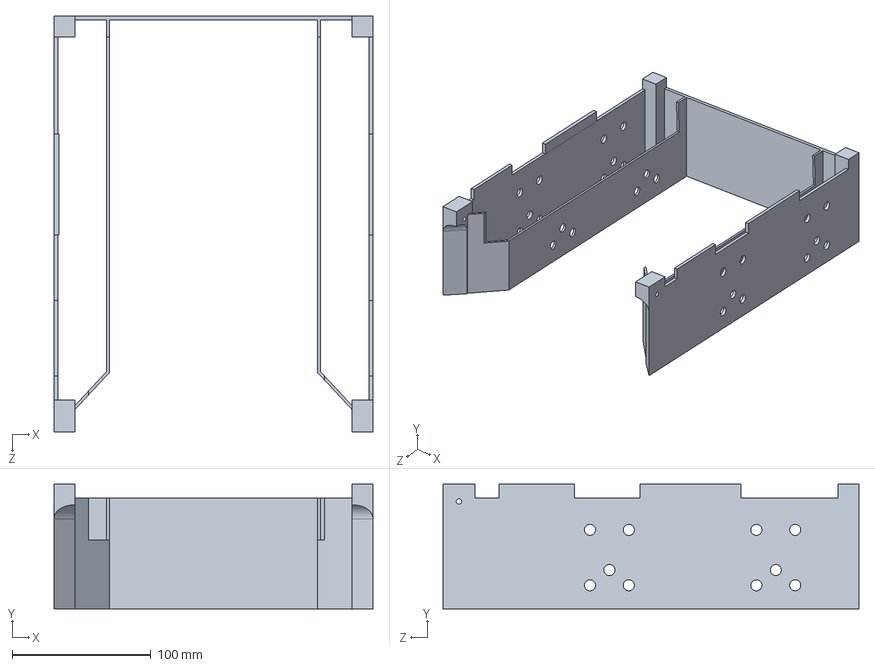
[picture p81: CAD file, 2025-01-23]
cad-files/chassis.SLDPRT
230.0 x 90.0 x 300.0 mm
