serhalahmad/unibots/cad-files/gearbox test/6mmshaft.STL

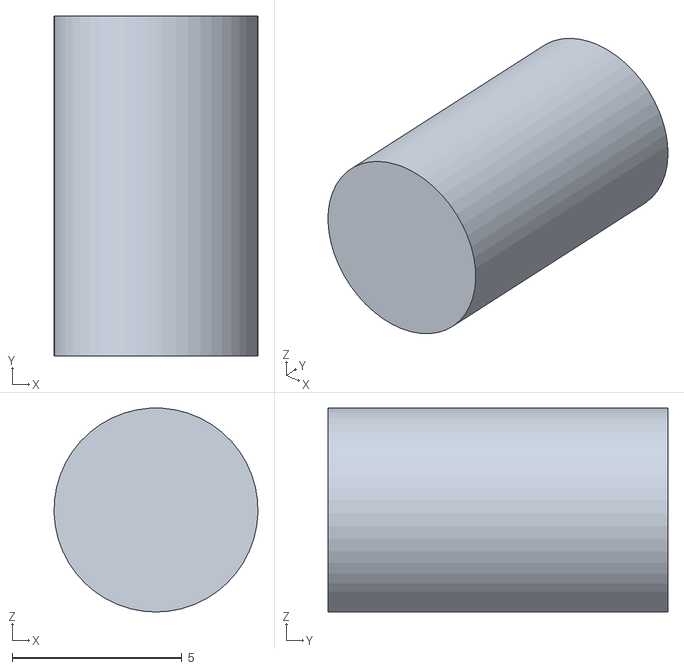
[picture p82: CAD file, 2025-02-14]
cad-files/gearbox test/6mmshaft.STL
6.00 x 10.0 x 6.00
