serhalahmad/unibots/cad-files/unibots chassis/beam1.SLDPRT.STL

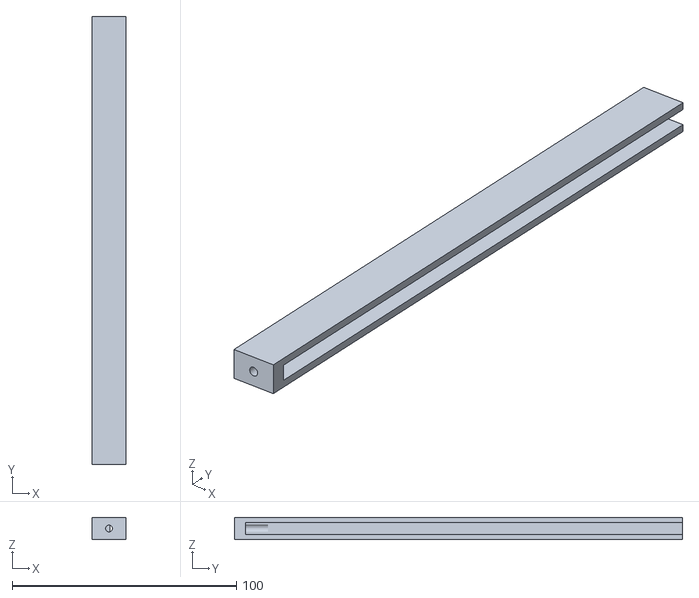
[picture p83: CAD file, 2025-03-25]
cad-files/unibots chassis/beam1.SLDPRT.STL
15.0 x 200.0 x 10.0
