serhalahmad/unibots/cad-files/unibots v1/push door.SLDPRT

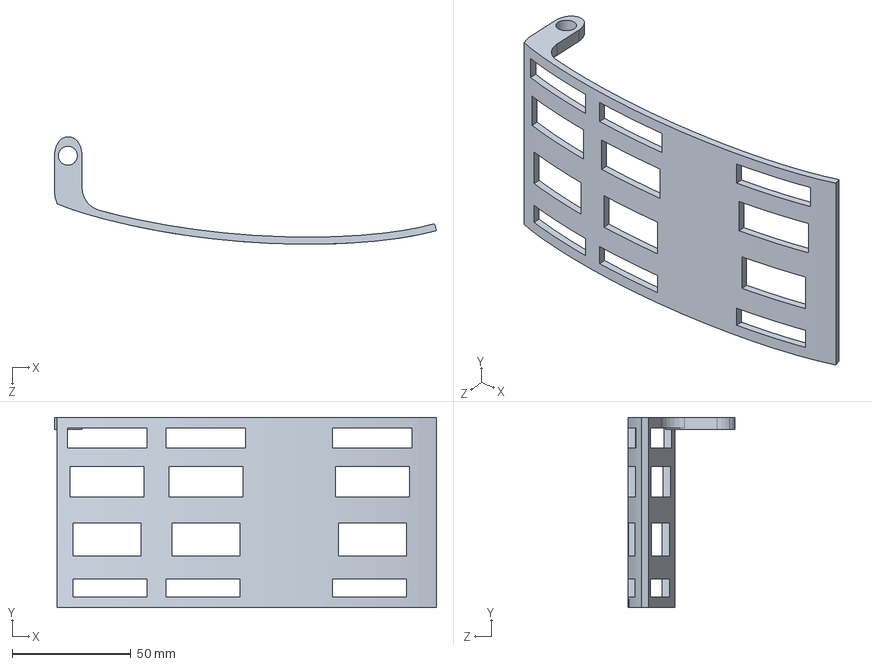
[picture p84: CAD file, 2025-01-23]
cad-files/unibots v1/push door.SLDPRT
160.6 x 80.0 x 45.1 mm
