serhalahmad/unibots/cad-files/gearbox test/Body2.stl

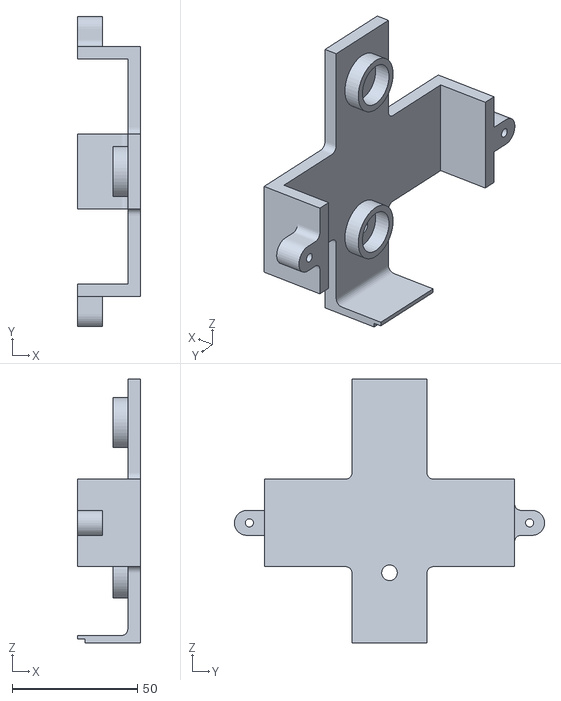
[picture p85: CAD file, 2025-02-14]
cad-files/gearbox test/Body2.stl
25.0 x 124.0 x 105.5
