serhalahmad/unibots/cad-files/plate.SLDPRT

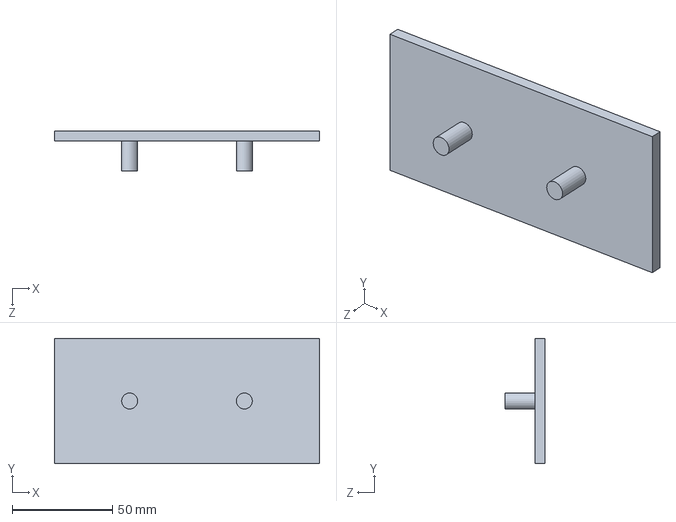
[picture p86: CAD file, 2025-01-23]
cad-files/plate.SLDPRT
132.2 x 62.4 x 20.0 mm
