serhalahmad/unibots/cad-files/unibots chassis/trapmechpart3.SLDPRT

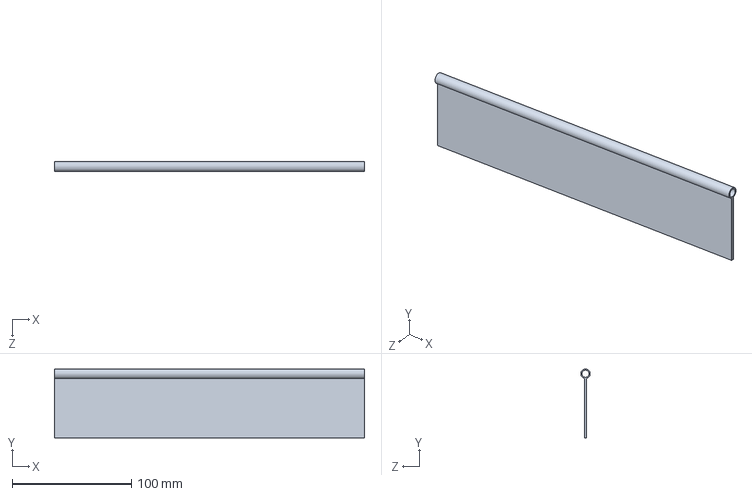
[picture p87: CAD file, 2025-03-25]
cad-files/unibots chassis/trapmechpart3.SLDPRT
260.0 x 57.8 x 7.98 mm
