serhalahmad/unibots/cad-files/unibots v1/chassis og.SLDPRT

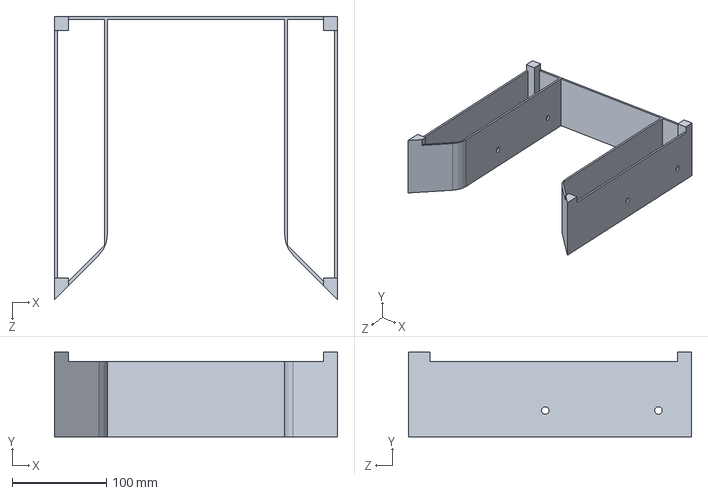
[picture p88: CAD file, 2025-01-23]
cad-files/unibots v1/chassis og.SLDPRT
300.0 x 90.0 x 300.0 mm
