serhalahmad/unibots/cad-files/gearbox test/motor gear.SLDPRT

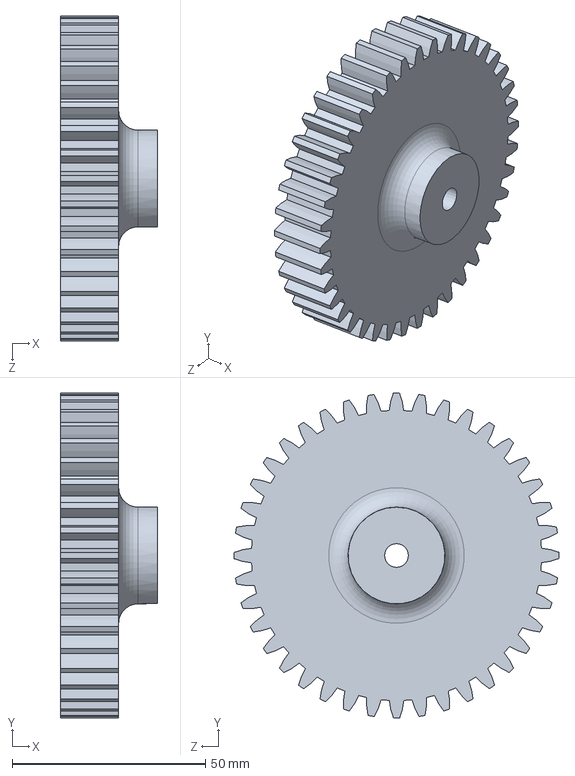
[picture p89: CAD file, 2025-02-14]
cad-files/gearbox test/motor gear.SLDPRT
25.0 x 84.0 x 84.0 mm
