serhalahmad/unibots/cad-files/gearbox test/Body1.stl

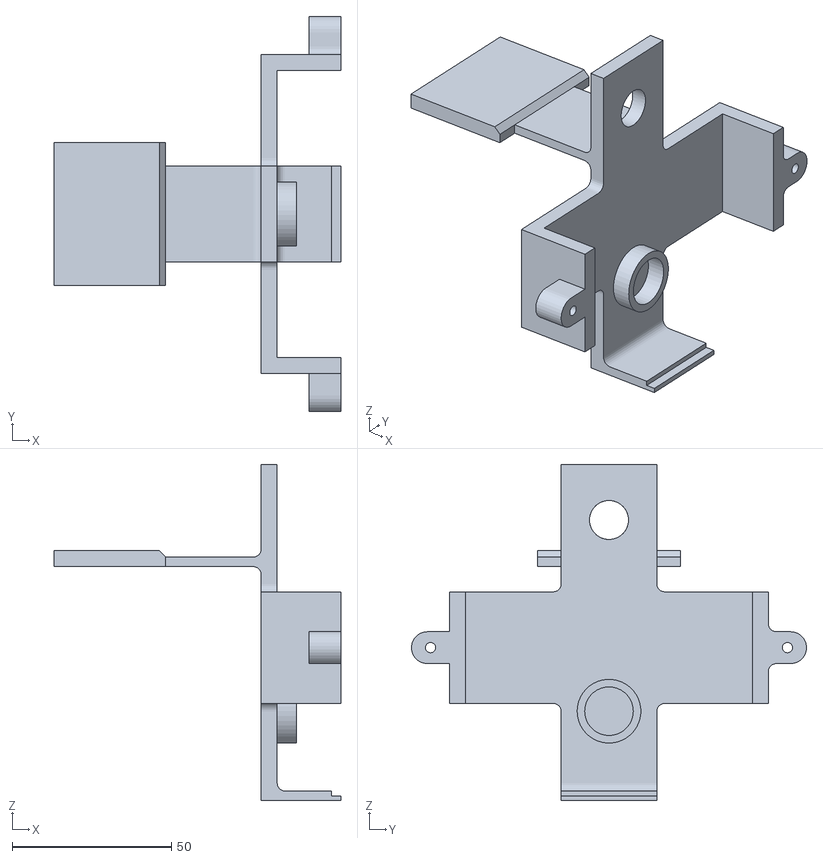
[picture p90: CAD file, 2025-02-14]
cad-files/gearbox test/Body1.stl
90.0 x 123.9 x 105.5
