serhalahmad/unibots/cad-files/gearbox test/motor asembly tes.SLDPRT

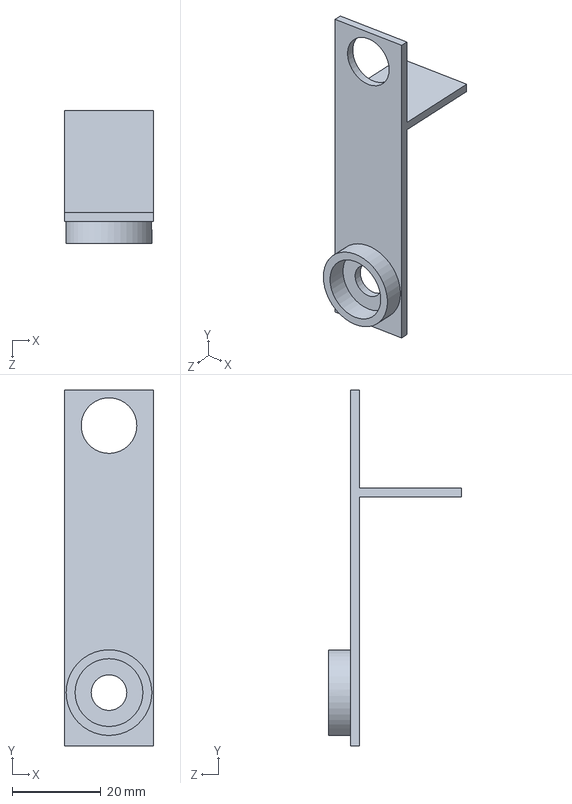
[picture p91: CAD file, 2025-02-14]
cad-files/gearbox test/motor asembly tes.SLDPRT
20.0 x 80.0 x 30.0 mm
