serhalahmad/unibots/cad-files/unibots chassis/pingpong-leftrightwall.SLDPRT

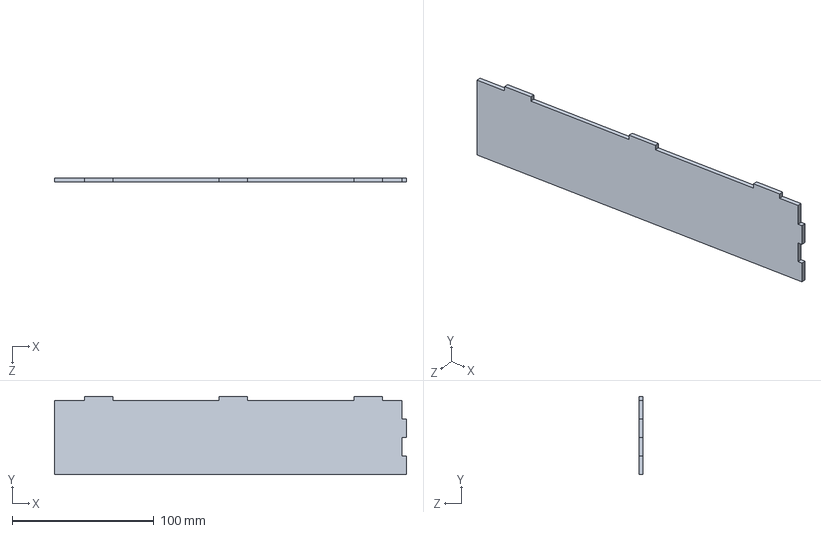
[picture p92: CAD file, 2025-03-25]
cad-files/unibots chassis/pingpong-leftrightwall.SLDPRT
248.1 x 55.0 x 3.00 mm
