serhalahmad/unibots/cad-files/unibots chassis/diagonalwall1.SLDPRT

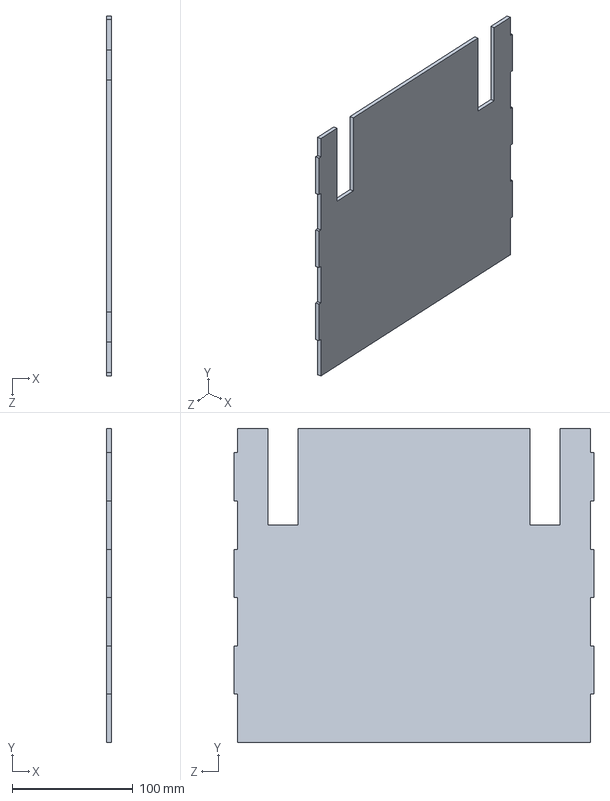
[picture p93: CAD file, 2025-03-25]
cad-files/unibots chassis/diagonalwall1.SLDPRT
4.00 x 260.0 x 298.0 mm
