serhalahmad/unibots/cad-files/unibots chassis/side wall.SLDPRT

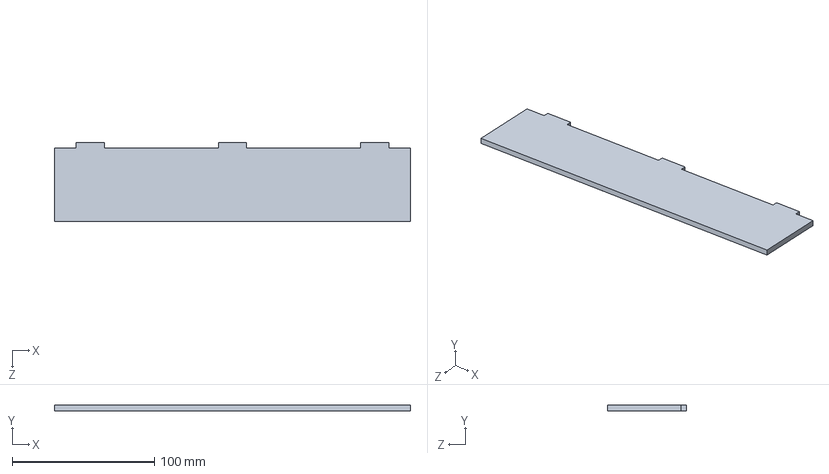
[picture p94: CAD file, 2025-03-25]
cad-files/unibots chassis/side wall.SLDPRT
250.0 x 4.00 x 55.5 mm
