serhalahmad/unibots/cad-files/unibots chassis/flatwall.SLDPRT

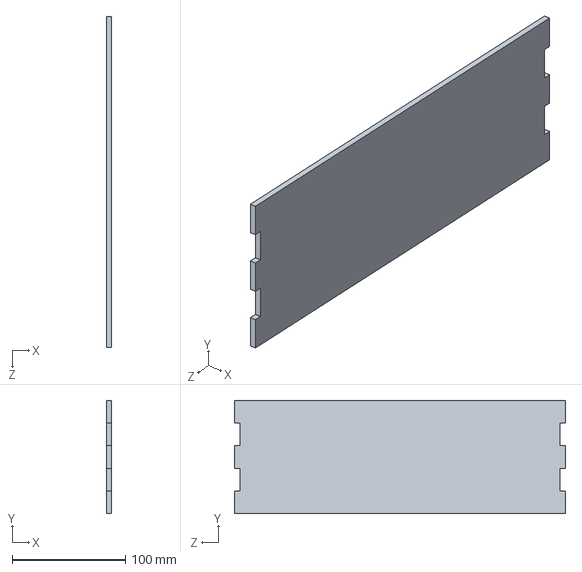
[picture p95: CAD file, 2025-03-25]
cad-files/unibots chassis/flatwall.SLDPRT
4.00 x 100.0 x 292.0 mm
