serhalahmad/unibots/cad-files/unibots chassis/trapdoor beam.SLDPRT

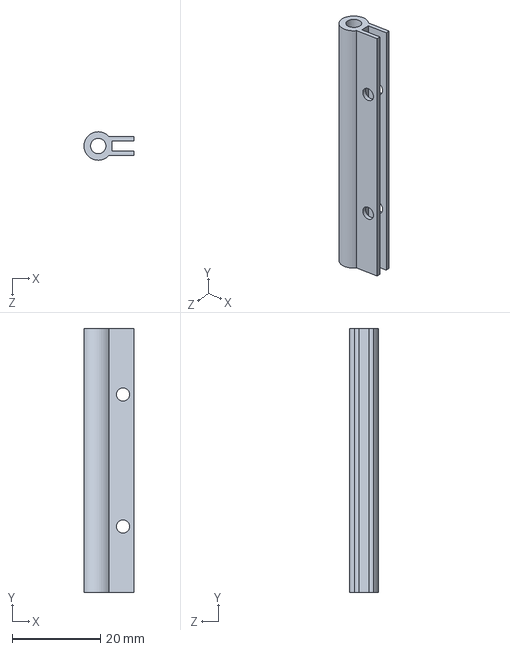
[picture p96: CAD file, 2025-03-25]
cad-files/unibots chassis/trapdoor beam.SLDPRT
11.4 x 60.0 x 6.49 mm
