serhalahmad/unibots/cad-files/unibots chassis/rugbymech2.SLDPRT

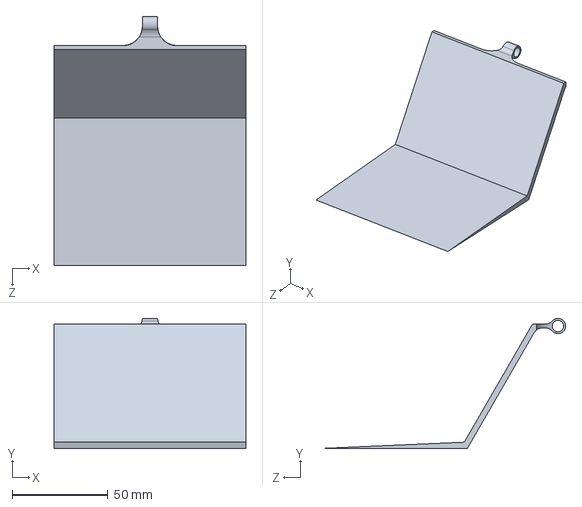
[picture p97: CAD file, 2025-03-25]
cad-files/unibots chassis/rugbymech2.SLDPRT
100.0 x 67.8 x 129.8 mm
