serhalahmad/unibots/cad-files/unibots chassis/trapdoorwall.SLDPRT

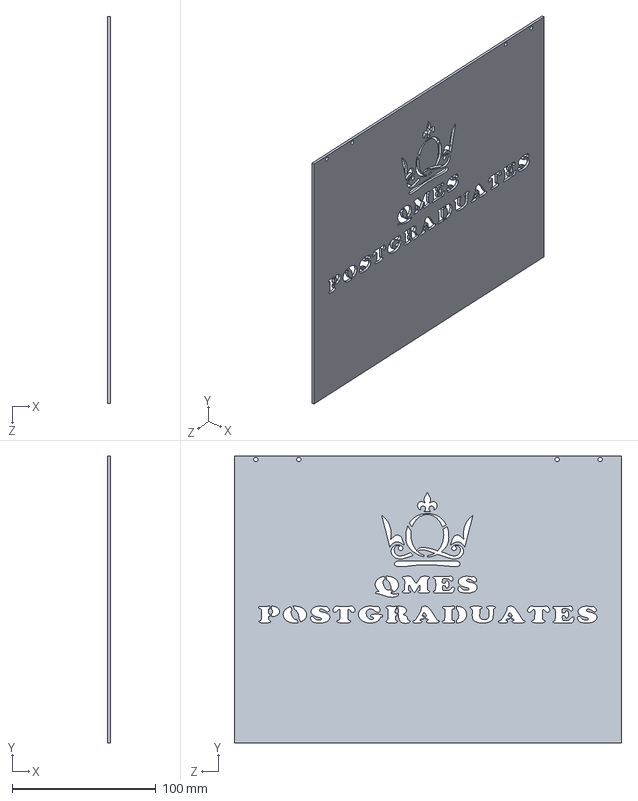
[picture p98: CAD file, 2025-03-25]
cad-files/unibots chassis/trapdoorwall.SLDPRT
2.00 x 200.0 x 270.0 mm
