serhalahmad/unibots/cad-files/unibots chassis/trapmechpart2.SLDPRT

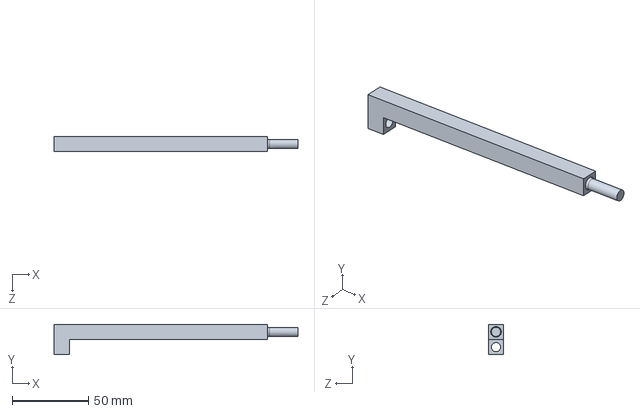
[picture p99: CAD file, 2025-03-25]
cad-files/unibots chassis/trapmechpart2.SLDPRT
160.0 x 20.0 x 10.0 mm
