serhalahmad/unibots/cad-files/unibots chassis/motorsupport.DXF

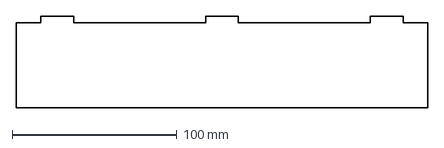
[picture p100: CAD file, 2025-03-25]
cad-files/unibots chassis/motorsupport.DXF
250.0 x 55.5 mm
